zengwangfa/2019-Electronic-Design-Competition/docs/DataSheet/NB-IOT/3.8V供电接线原理图.png

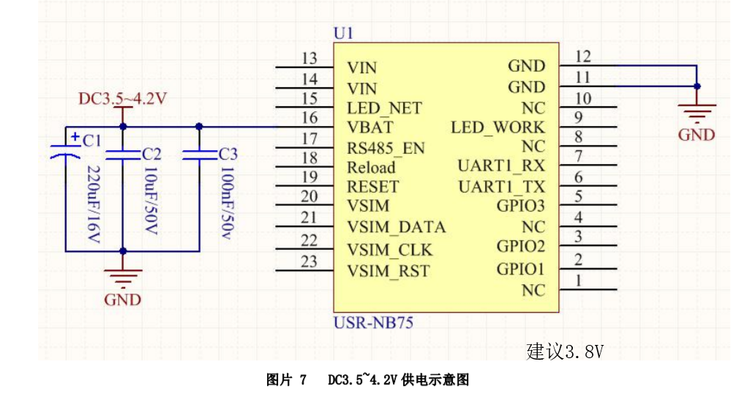
docs/DataSheet/NB-IOT/3.8V供电接线原理图.png
