zengwangfa/2019-Electronic-Design-Competition/docs/DataSheet/NB-IOT/3.8v供电注意事项.png

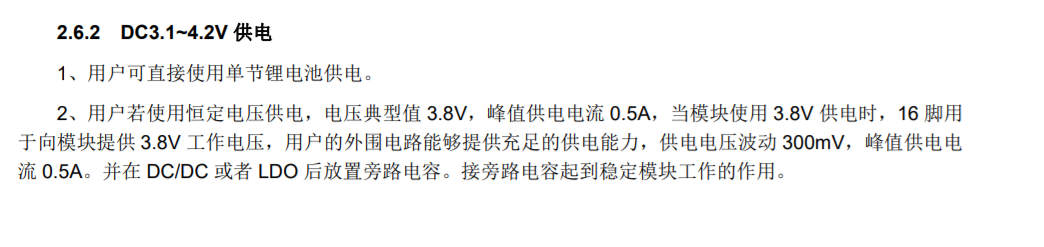
docs/DataSheet/NB-IOT/3.8v供电注意事项.png
