zengwangfa/2019-Electronic-Design-Competition/docs/DataSheet/NB-IOT/SIM卡引脚位.png

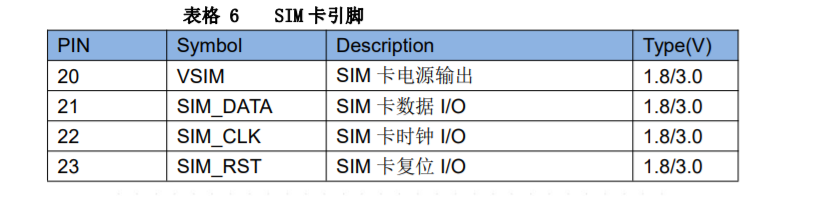
docs/DataSheet/NB-IOT/SIM卡引脚位.png
