zengwangfa/2019-Electronic-Design-Competition/docs/DataSheet/NB-IOT/串口.png

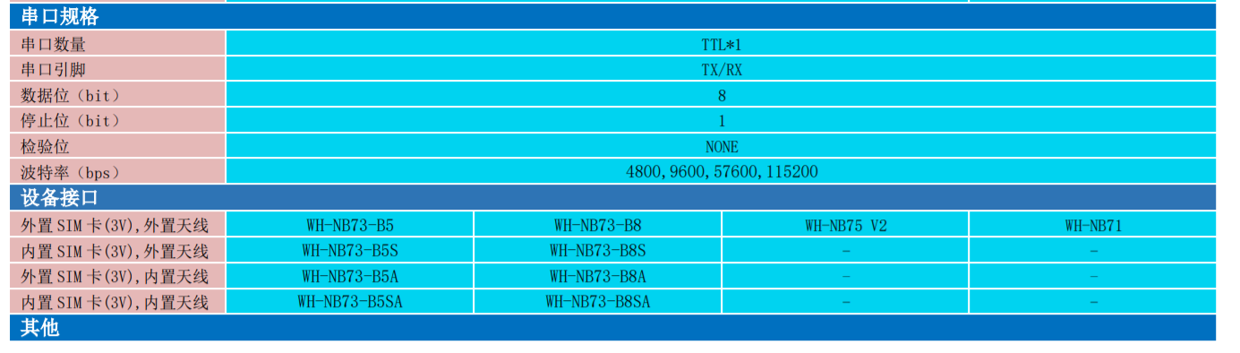
docs/DataSheet/NB-IOT/串口.png
