zengwangfa/2019-Electronic-Design-Competition/docs/DataSheet/NB-IOT/基本参数.png

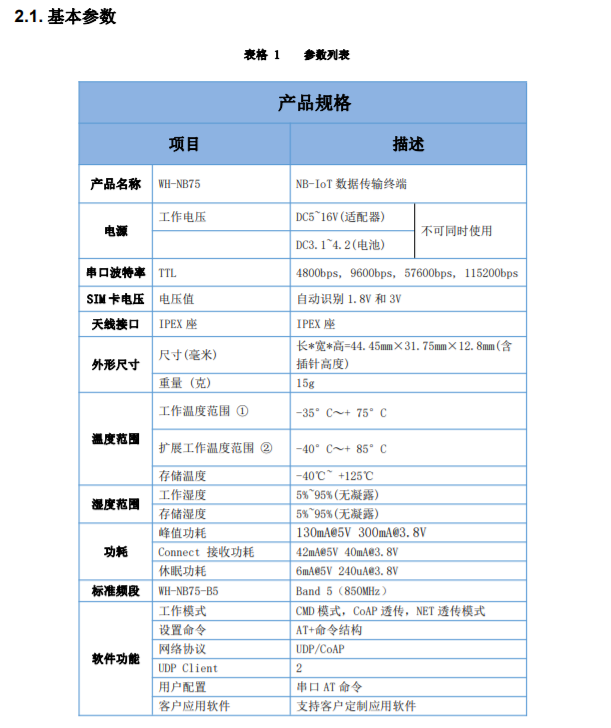
docs/DataSheet/NB-IOT/基本参数.png
