zengwangfa/2019-Electronic-Design-Competition/docs/DataSheet/NB-IOT/透传云注册.png

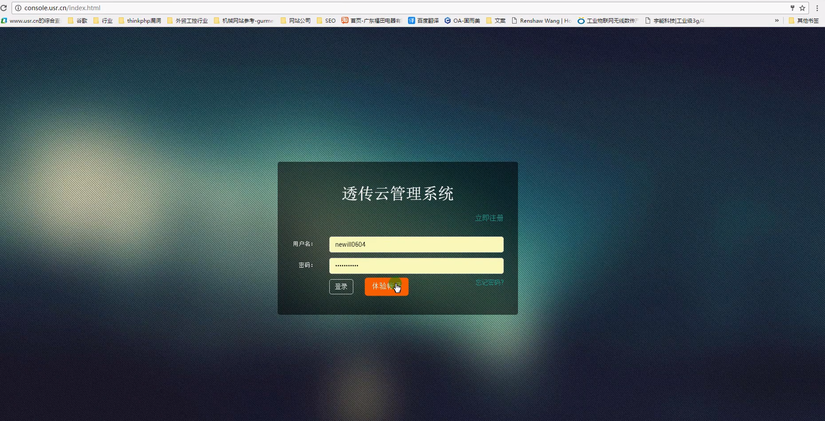
docs/DataSheet/NB-IOT/透传云注册.png
