zengwangfa/2019-Electronic-Design-Competition/docs/pictures/2017年全国大学生电子设计竞赛综合测评题.jpg

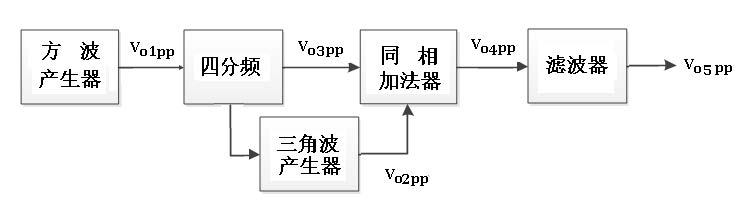
docs/pictures/2017年全国大学生电子设计竞赛综合测评题.jpg
