zengwangfa/2019-Electronic-Design-Competition/docs/pictures/2017综合测评题 (1).jpg

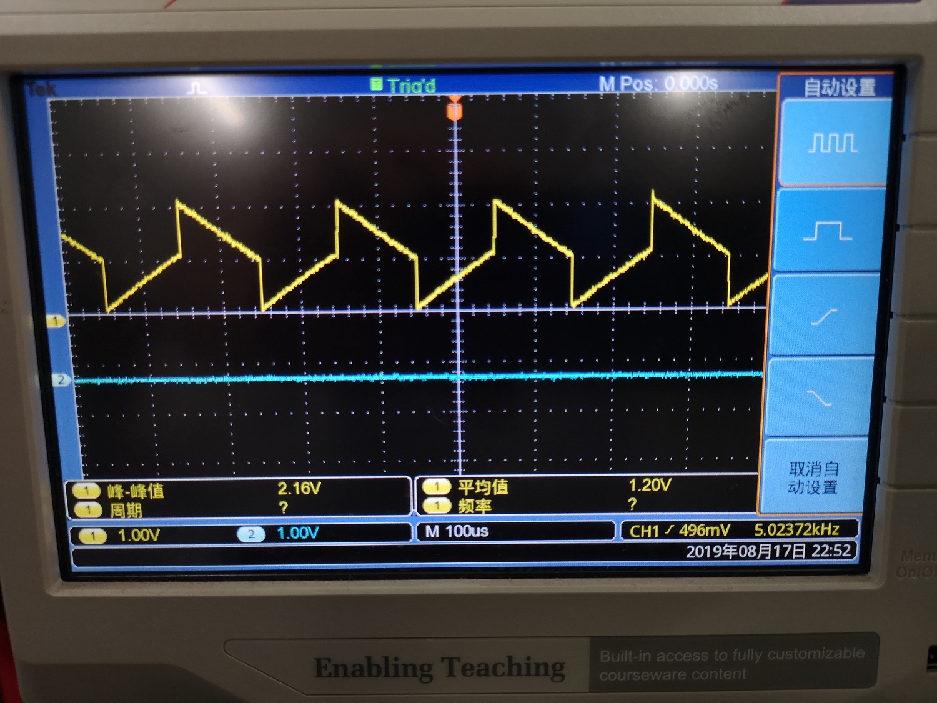
docs/pictures/2017综合测评题 (1).jpg
