zengwangfa/2019-Electronic-Design-Competition/docs/pictures/hmi/paper_hmi.gif

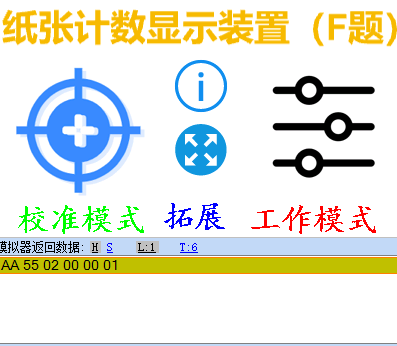
docs/pictures/hmi/paper_hmi.gif
