zengwangfa/2019-Electronic-Design-Competition/hmi/picture & font/picture (2).png

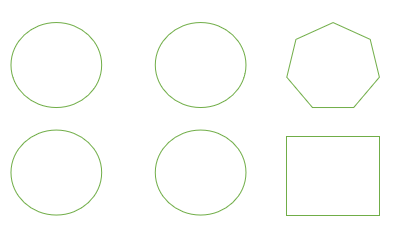
hmi/picture & font/picture (2).png
