zengwangfa/2019-Electronic-Design-Competition/hmi/picture & font/picture (3).png

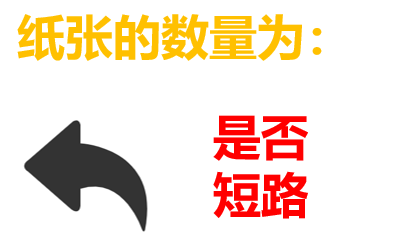
hmi/picture & font/picture (3).png
