zengwangfa/2019-Electronic-Design-Competition/hmi/picture & font/picture (4).png

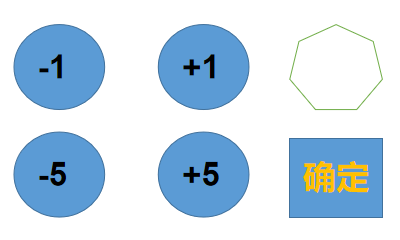
hmi/picture & font/picture (4).png
