zengwangfa/2019-Electronic-Design-Competition/hmi/picture & font/下降 (1).png

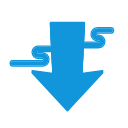
hmi/picture & font/下降 (1).png
