zengwangfa/2019-Electronic-Design-Competition/hmi/picture & font/减 (1) - 副本.png

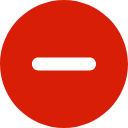
hmi/picture & font/减 (1) - 副本.png
