zengwangfa/2019-Electronic-Design-Competition/hmi/picture & font/加.png

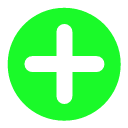
hmi/picture & font/加.png
