zengwangfa/2019-Electronic-Design-Competition/hmi/picture & font/升级 (4).png

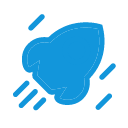
hmi/picture & font/升级 (4).png
