zengwangfa/2019-Electronic-Design-Competition/hmi/picture & font/原材料.png

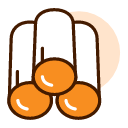
hmi/picture & font/原材料.png
