zengwangfa/2019-Electronic-Design-Competition/hmi/picture & font/手势单击系列.png

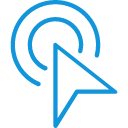
hmi/picture & font/手势单击系列.png
