zengwangfa/2019-Electronic-Design-Competition/hmi/picture & font/打印机.png

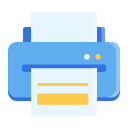
hmi/picture & font/打印机.png
