zengwangfa/2019-Electronic-Design-Competition/hmi/picture & font/按钮 (1).png

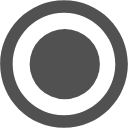
hmi/picture & font/按钮 (1).png
