zengwangfa/2019-Electronic-Design-Competition/hmi/picture & font/纸币 (1).png

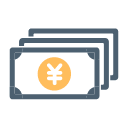
hmi/picture & font/纸币 (1).png
