zengwangfa/2019-Electronic-Design-Competition/hmi/picture & font/超级玛丽3.jpg

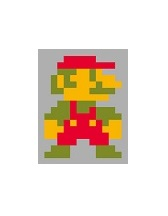
hmi/picture & font/超级玛丽3.jpg
