zengwangfa/2019-Electronic-Design-Competition/matlab/电容1.png

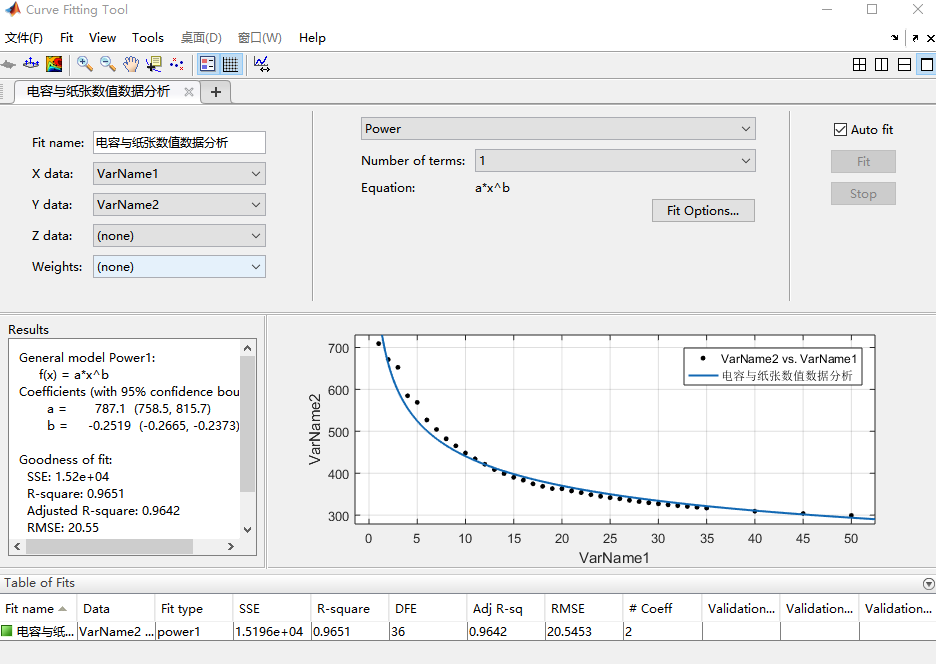
matlab/电容1.png
