zengwangfa/2019-Electronic-Design-Competition/matlab/电容2.png

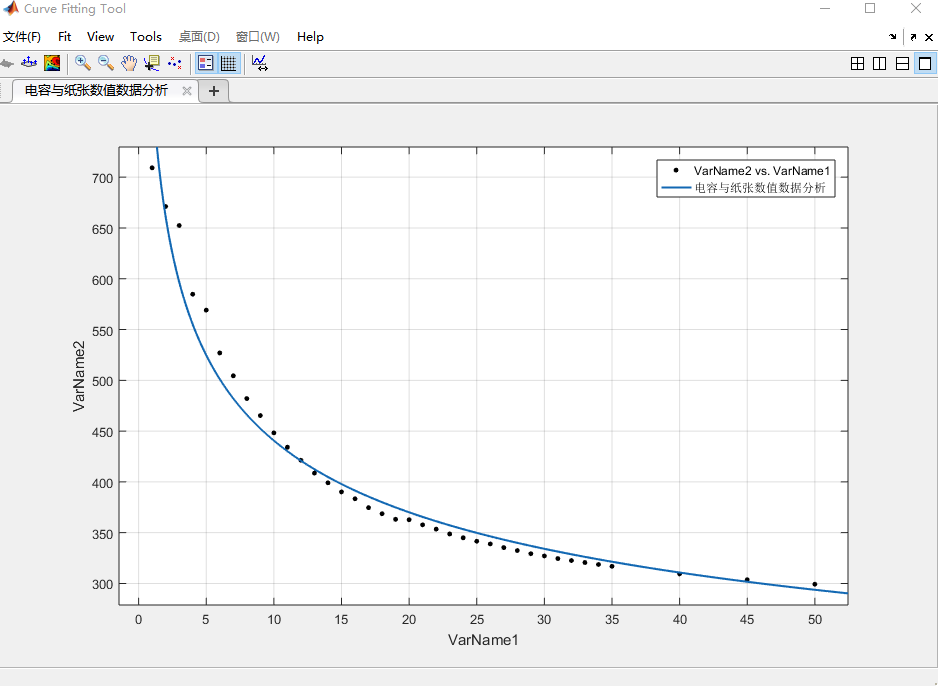
matlab/电容2.png
