zengwangfa/2019-Electronic-Design-Competition/matlab/纸张1.png

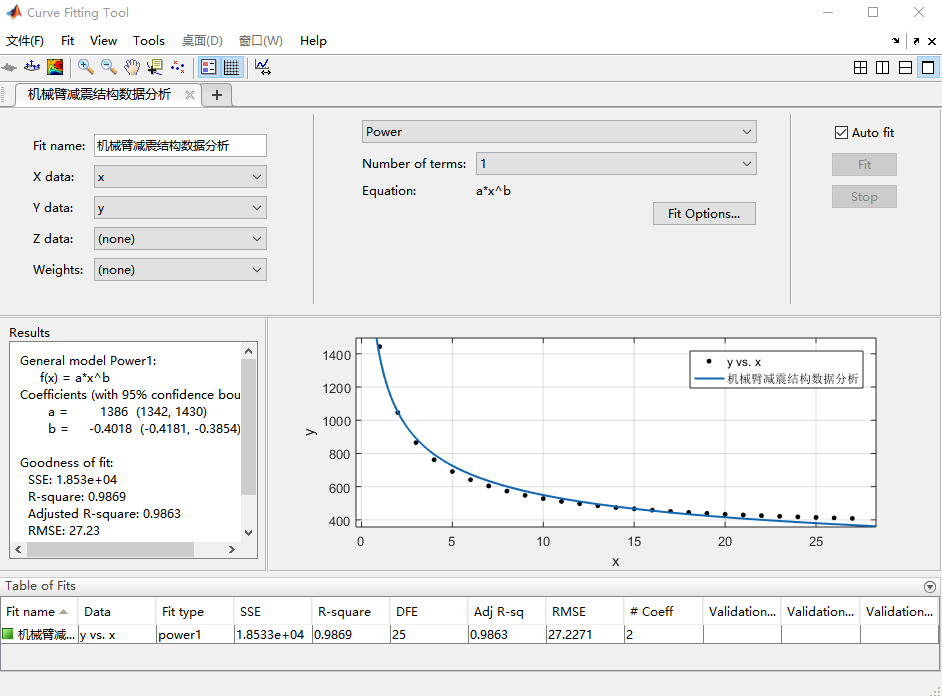
matlab/纸张1.png
