zengwangfa/2019-Electronic-Design-Competition/matlab/纸张2.png

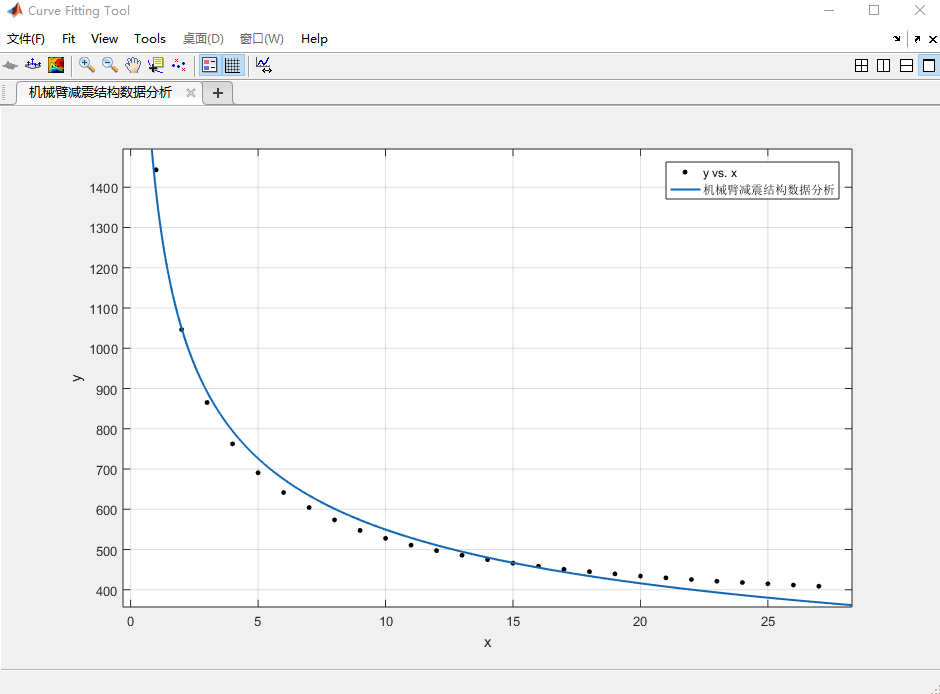
matlab/纸张2.png
