zengwangfa/2019-Electronic-Design-Competition/docs/pictures/debug.png

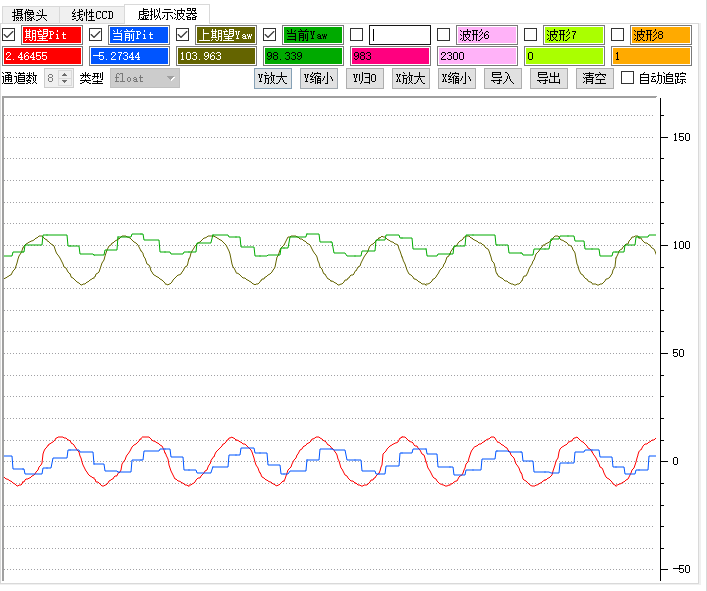
docs/pictures/debug.png
