zengwangfa/2019-Electronic-Design-Competition/others/software for development board/rt-thread-master/bsp/stm32f40x/applications/sensor.c

/*
 * servo.c
 *
 *  Created on: 2019年2月30日
 *      Author: zengwangfa
 *      Notes:  传感器设备【深度传感器、CPU参数、ADC电压】
 */
 
 #define LOG_TAG    "sensor"
#include "sensor.h"
#include <rtthread.h>
#include <elog.h>
#include <string.h>
#include "drv_MS5837.h"
#include "gyroscope.h"
#include "flash.h"
#include "stdio.h"
#include "drv_i2c.h"
#include "drv_adc.h"
#include "drv_cpu_temp.h"
#include "drv_cpuusage.h"
#include "filter.h"
#include "drv_spl1301.h"

/*----------------------- Variable Declarations -----------------------------*/
char *Depth_Sensor_Name[3] = {"MS5837","SPL1301","null"};

Sensor_Type Sensor;//传感器参数
		float temp_current = 0.0f;

/*----------------------- Function Implement --------------------------------*/
/**
  * @brief  sensor_lowSpeed_thread_entry(低速获取传感器任务函数)
  * @param  void* parameter
  * @retval None
  * @notice 
  */
void sensor_lowSpeed_thread_entry(void* parameter)
{
		uint8 cpu_usage_major, cpu_usage_minor; //整数位、小数位

		rt_thread_mdelay(1000);//等待3s系统稳定再获取数据

		while(1)
		{
			
				Sensor.CPU.Temperature = get_cpu_temp();           //获取CPU温度
				Sensor.PowerSource.Voltage = get_voltage_value();  //获取电源电压值
//				if(Sensor.PowerSource.Voltage > 6.0f ){							//当未接入电源时，不检测电流值
//						
//						Sensor.PowerSource.Current = get_current_value();  //获取INA169电流值
//						temp_current = Sensor.PowerSource.Current ;
//						Sensor.PowerSource.Current = KalmanFilter(&Sensor.PowerSource.Current);
//						 //电流值 进行卡尔曼滤波【该卡尔曼滤波调节r的值，滞后性相对较大】
//				}
				cpu_usage_get(&cpu_usage_major, &cpu_usage_minor); //获取CPU使用率
				Sensor.CPU.Usage = cpu_usage_major + (float)cpu_usage_minor/100;
			

				rt_thread_mdelay(100);
		}
}

/**
  * @brief  sensor_highSpeed_thread_entry(高速获取传感器任务函数)
  * @param  void* parameter
  * @retval None
  * @notice 
  */


void sensor_highSpeed_thread_entry(void* parameter)
{

		rt_thread_mdelay(1000);//等待3s系统稳定再获取数据
	
		while(1)
		{
			
				//JY901_Convert(&Sensor.JY901); //JY901数据转换
				//Depth_Sensor_Data_Convert();  //深度数据转换

				rt_thread_mdelay(20);
		}
}



/*******************************线程初始化*******************************************/
int sensor_thread_init(void)
{
    rt_thread_t sensor_lowSpeed_tid; //低速获取的传感器放入接口
	  rt_thread_t sensor_highSpeed_tid;//高速获取的传感器放入接口
		/*创建动态线程*/
    sensor_lowSpeed_tid = rt_thread_create("sensor",  //线程名称
                    sensor_lowSpeed_thread_entry,		 //线程入口函数【entry】
                    RT_NULL,							   //线程入口函数参数【parameter】
                    2048,										 //线程栈大小，单位是字节【byte】
                    30,										 	 //线程优先级【priority】
                    10);										 //线程的时间片大小【tick】= 100ms

	  sensor_highSpeed_tid = rt_thread_create("sensor",  //线程名称
                    sensor_highSpeed_thread_entry,		 //线程入口函数【entry】
                    RT_NULL,							   //线程入口函数参数【parameter】
                    2048,										 //线程栈大小，单位是字节【byte】
                    10,										 	 //线程优先级【priority】
                    3);										 //线程的时间片大小【tick】= 100ms

    if (sensor_lowSpeed_tid != RT_NULL && sensor_highSpeed_tid != RT_NULL){
			



				if(adc_init()){ log_i("Adc_Init()");}//ADC电压采集初始化

//				rt_thread_startup(sensor_lowSpeed_tid);
//				rt_thread_startup(sensor_highSpeed_tid);
		}
		return 0;
}
//INIT_APP_EXPORT(sensor_thread_init);


void Depth_Sensor_Data_Convert(void)//深度传感器数据转换
{
		static uint32 value[10] = {0};
		static uint8 ON_OFF = 0; //自锁开关
		static uint8 i = 0;
		
		if(SPL1301 == Sensor.DepthSensor.Type){  //歌尔 SPL1301
				spl1301_get_raw_temp();
				spl1301_get_raw_pressure();//传感器数据转换
				
				if(ON_OFF == 0){
						ON_OFF = 1;
						Sensor.DepthSensor.Init_PessureValue = get_spl1301_pressure();//获取初始化数据
				}
				for(i = 0;i < 10;i++){
						value[i++] = get_spl1301_pressure();//获取1次数据
				}
				Sensor.DepthSensor.Temperature = get_spl1301_temperature();
				Sensor.DepthSensor.PessureValue = Bubble_Filter(value);
								 				                              /* 深度数值 单位为cm   定标系数为 1.3 单位/cm */
				Sensor.DepthSensor.Depth = ((Sensor.DepthSensor.PessureValue - Sensor.DepthSensor.Init_PessureValue)/20);		
			 
		}
		else if(MS5837 == Sensor.DepthSensor.Type){ //使用MS5837
			
				if(ON_OFF == 0 ){
						ON_OFF = 1; //自锁开关																							       
						Sensor.DepthSensor.Init_PessureValue = get_ms5837_pressure();//获取初始化数据
				}		 
						
				Sensor.DepthSensor.PessureValue = get_ms5837_pressure();
				Sensor.DepthSensor.Temperature  = get_ms5837_temperature();

				//理想状态，深度传感器的压力值理应越来越大
				if(Sensor.DepthSensor.Init_PessureValue - Sensor.DepthSensor.PessureValue >= 1 && \
					 Sensor.DepthSensor.Init_PessureValue - Sensor.DepthSensor.PessureValue <= 5 ){	//若深度传感器 当前值逐渐变小，则判定为发生漂移，令初值等于当前值
			
						Sensor.DepthSensor.Init_PessureValue = Sensor.DepthSensor.PessureValue;
				}
					 				                              /* 深度数值 单位为cm   定标系数为 1.95 单位/cm */
				Sensor.DepthSensor.Depth = ((Sensor.DepthSensor.PessureValue - Sensor.DepthSensor.Init_PessureValue)/1.95f);			
		}

}


/* 打印传感器信息 */
void print_sensor_info(void)
{
		log_i("    variable        |  value");
		log_i("--------------------|-----------");
	
		log_i("      Roll          |  %+0.3f",Sensor.JY901.Euler.Roll);
		log_i("      Pitch         |  %+0.3f",Sensor.JY901.Euler.Pitch);
		log_i("      Yaw           |  %+0.3f",Sensor.JY901.Euler.Yaw);
		log_i("--------------------|-----------");
		log_i("      Acc.x         |  %+0.3f",Sensor.JY901.Acc.x);
		log_i("      Acc.y         |  %+0.3f",Sensor.JY901.Acc.y);//
		log_i("      Acc.z         |  %+0.3f",Sensor.JY901.Acc.z);//
		log_i("--------------------|-----------");
		log_i("      Gyro.x        |  %+0.3f",Sensor.JY901.Gyro.x);
		log_i("      Gyro.y        |  %+0.3f",Sensor.JY901.Gyro.y);//	
		log_i("      Gyro.z        |  %+0.3f",Sensor.JY901.Gyro.z);//	
		log_i("  JY901_Temperature |  %+0.3f",Sensor.JY901.Temperature);//					

	
		log_i("--------------------|-----------");
		log_i("     Voltage        |  %0.3f",Sensor.PowerSource.Voltage); //电压
		log_i("     Current        |  %0.3f",Sensor.PowerSource.Current); //电流
		log_i("--------------------|-----------");
		log_i("  Depth Sensor Type |  %s",Depth_Sensor_Name[Sensor.DepthSensor.Type]); //深度传感器类型
		log_i(" Water Temperature  |  %0.3f",Sensor.DepthSensor.Temperature);    //水温
		log_i("sensor_Init_Pressure|  %0.3f",Sensor.DepthSensor.Init_PessureValue); //深度传感器初始压力值	
		log_i("   sensor_Pressure  |  %0.3f",Sensor.DepthSensor.PessureValue); 		 //深度传感器当前压力值	
		log_i("     Depth          |  %0.3f",Sensor.DepthSensor.Depth); 									 //深度值
		log_i("--------------------|-----------");	
		log_i("    CPU.Usages      |  %0.3f",	Sensor.CPU.Temperature); //CPU温度
		log_i("   CPU.Temperature  |  %0.3f",	Sensor.CPU.Usage); 			 //CPU使用率

		

}
MSH_CMD_EXPORT(print_sensor_info, printf gysocope & PowerSource & pressure);



/*【深度传感器】 修改 【类型】MSH方法 */
static int set_depth_sensor_type(int argc, char **argv) //只能是 0~3.0f
{
    int result = 0;
    if (argc != 2){ //6个推进器
        log_e("Error! Proper Usage: set_depth_sensor_type <ms5837/spl1301/null>");
				result = -RT_ERROR;
        goto _exit;
    }
		
	  if( !strcmp(argv[1],"ms5837") ) {
				 
				Sensor.DepthSensor.Type = MS5837; //
				Flash_Update();
	
				log_i("Sensor.DepthSensor.Type :%s",Depth_Sensor_Name[Sensor.DepthSensor.Type]);
				log_i("Please reboot now");		
		}
	  else if( !strcmp(argv[1],"spl1301") ) {
				 
				Sensor.DepthSensor.Type = SPL1301; //
				Flash_Update();

				log_i("Sensor.DepthSensor.Type :%s",Depth_Sensor_Name[Sensor.DepthSensor.Type]);
				log_i("Please reboot now");				
		}	

	  else if( !strcmp(argv[1],"null") ) {
				 
				Sensor.DepthSensor.Type = DS_NULL; //无深度传感器
				Flash_Update();

				log_i("Sensor.DepthSensor.Type :%s",Depth_Sensor_Name[Sensor.DepthSensor.Type]);
				log_i("Please reboot now");				
		}				
		else {
				log_e("Error! Input Error!");
		}
_exit:
    return result;
}
MSH_CMD_EXPORT(set_depth_sensor_type,depth_sensor_type_set <ms5837/spl1301/null> );



/*【电源容量】 修改 【容量】MSH方法 */
static int set_battery_capacity(int argc, char **argv)
{
    int result = 0;
    if (argc != 2){ //6个推进器
        log_e("Error! Proper Usage: set_battery_capacity <2s/3s/4s/6s> % ");
				result = -RT_ERROR;
        goto _exit;
    }
		
	  if( !strcmp(argv[1],"2s") ) {
				 
				Sensor.PowerSource.Capacity = 4.2*2; // 2s->8.4v的满电压
				Flash_Update();
	
				log_i("Sensor.PowerSource.Capacity :%f v",Sensor.PowerSource.Capacity);
		}		
	  else if( !strcmp(argv[1],"3s") ) {
				 
				Sensor.PowerSource.Capacity = 4.2*3; // 3s->12.6v的满电压
				Flash_Update();
	
				log_i("Sensor.PowerSource.Capacity :%f v",Sensor.PowerSource.Capacity);
		}
	  else if( !strcmp(argv[1],"4s") ) {
				 
				Sensor.PowerSource.Capacity = 4.2*4; // 4s->16.8v的满电压
				Flash_Update();

				log_i("Sensor.PowerSource.Capacity :%f v",Sensor.PowerSource.Capacity);
		}		
		
		else if( !strcmp(argv[1],"6s") ) {
				 
				Sensor.PowerSource.Capacity = 4.2*6; // 6s->25.2v的满电压
				Flash_Update();

				log_i("Sensor.PowerSource.Capacity :%f v",Sensor.PowerSource.Capacity);
		}		
		else {
				log_e("Error! Input Error!");
		}
_exit:
    return result;
}
MSH_CMD_EXPORT(set_battery_capacity,set_battery_capacity <2s/3s/4s/6s> );
