zengwangfa/2019-Electronic-Design-Competition/others/software for development board/rt-thread-master/bsp/stm32f40x/applications/sensor.h

#ifndef __SENSOR_H_
#define __SENSOR_H_

#include "DataType.h"


/* 打印传感器信息 */
void print_sensor_info(void);
void Depth_Sensor_Data_Convert(void);//深度传感器数据转换

extern char *Depth_Sensor_Name[3];


#endif
