zengwangfa/2019-Electronic-Design-Competition/others/software for development board/rt-thread-master/bsp/stm32f40x/drivers/drv_ano.c

/*
 * File      : drv_ano.c
 * COPYRIGHT (C) 2019 JMU Electronic Technology Association Team 
 *
 * Change Logs:
 * Date         Author          Notes
 * 2019.3				zengwangfa      匿名地面站(ANO_TC)通信协议移植v1.0
 * 
 * Attention: 接收只需要调用 -> ANO_DT_Data_Receive_Prepare(uint8 data);
 *【统一接口】发送只需要调用 -> ANO_SEND_StateMachine(void);
 *            保存参数需调用 -> void Save_Or_Reset_PID_Parameter(void);
 */
#include <rtdevice.h>
#include <elog.h>
#include "drv_ano.h"
#include "sys.h"
#include "PID.h"
#include "led.h"
#include "flash.h"
#include "gyroscope.h"
#include "rc_data.h"
#include "propeller.h"
#include <ioDevices.h>

/*---------------------- Constant / Macro Definitions -----------------------*/		

#define BYTE0(dwTemp)       ( *( (char *)(&dwTemp) + 0) )
#define BYTE1(dwTemp)       ( *( (char *)(&dwTemp) + 1) )
#define BYTE2(dwTemp)       ( *( (char *)(&dwTemp) + 2) )
#define BYTE3(dwTemp)       ( *( (char *)(&dwTemp) + 3) )
	


#define HardwareType 	0.00  //硬件种类  00为其他硬件版本
#define HardwareVER 	2.00  //硬件版本
#define SoftwareVER 	7.50  //软件版本  7月5日
#define ProtocolVER 	1  		//协议版本
#define BootloaderVER 1  		//Bootloader版本
/*----------------------- Variable Declarations. -----------------------------*/

extern rt_device_t debug_uart_device;	
extern float  volatge;
extern ReceiveData_Type ReceiveData;

Vector3f_pid PID_Parameter[PID_USE_NUM]={0};
uint8 data_to_send[50];//ANO地面站发送数据缓冲
uint8 ANO_Send_PID_Flag[6]={0};//PID发送标志位

uint8 Sort_PID_Cnt=0;
uint8 Sort_PID_Flag=0; //PID状态标志位：1存FLASH  2复位原始数据


//---------------这里是分隔符↓↓↓↓↓↓↓↓↓↓<以下为接收 函数>↓↓↓↓↓↓↓↓↓↓这里是分隔符------------------//
/*******************************************
* 函 数 名：ANO_DT_Data_Receive_Prepare
* 功    能：ANO地面站数据解析
* 输入参数：串口循环传入的一个数据data
* 返 回 值：none
* 注    意：none
********************************************/
void ANO_DT_Data_Receive_Prepare(uint8 data)//ANO地面站数据解析
{
		static uint8 RxBuffer[50];
		static uint8 _data_len = 0,_data_cnt = 0;
		static uint8 state = 0;
		if(state==0&&data==0xAA)//帧头1
		{
				state=1;
				RxBuffer[0]=data;
		}
		else if(state==1&&data==0xAF)//帧头2
		{
				state=2;
				RxBuffer[1]=data;
		}
		else if(state==2&&data<0XF1)//功能字节
		{
				state=3;
				RxBuffer[2]=data;
		}
		else if(state==3&&data<50)//有效数据长度
		{
				state = 4;
				RxBuffer[3]=data;
				_data_len = data;
				_data_cnt = 0;
		}
		else if(state==4&&_data_len>0)//数据接收
		{
				_data_len--;
				RxBuffer[4+_data_cnt++]=data;
				if(_data_len==0)
					state = 5;
		}
		else if(state==5)//校验和
		{
				state = 0;
				RxBuffer[4+_data_cnt]=data;
				ANO_DT_Data_Receive_Anl(RxBuffer,_data_cnt+5);//数据解析
		}
		else state = 0;
}



/*******************************************
* 函 数 名：ANO_DT_Send_Check
* 功    能：ANO地面站和校验
* 输入参数：head 功能字
						check_num 校验和
* 返 回 值：none
* 注    意：none
********************************************/
static void ANO_DT_Send_Check(uint8 head, uint8 check_sum)
{
		uint8 sum = 0,i=0;
		data_to_send[0]=0xAA;
		data_to_send[1]=0xAA;
		data_to_send[2]=0xEF;
		data_to_send[3]=2;
		data_to_send[4]=head;
		data_to_send[5]=check_sum;
		for(i=0;i<6;i++){
				sum += data_to_send[i];
		}
		data_to_send[6]=sum;
		rt_device_write(debug_uart_device, 0,data_to_send, 7);    //发送后命令

}

/*******************************************
* 函 数 名：ANO_DT_Data_Receive_Anl
* 功    能：ANO数据解析
* 输入参数：data_buf: 数据包
						num: 数据包大小
* 返 回 值：none
* 注    意：none
********************************************/
void ANO_DT_Data_Receive_Anl(uint8 *data_buf,uint8 num)
{
		uint8 sum = 0,i=0;
		for(i=0;i<(num-1);i++)  sum += *(data_buf+i);
		if(!(sum==*(data_buf+num-1)))    return; //判断sum
		if(!(*(data_buf)==0xAA && *(data_buf+1)==0xAF))     return;//判断帧头
		if(*(data_buf+2)==0x01)
		{
				if(*(data_buf+4)==0x01) {;}
				if(*(data_buf+4)==0x02) {;}
				if(*(data_buf+4)==0x03) {;}
		}
		
		if(*(data_buf+2)==0x02)
		{
				if(*(data_buf+4)==0x01)		//读取当前PID参数
				{
						ANO_Send_PID_Flag[0]=1;
						ANO_Send_PID_Flag[1]=1;
						ANO_Send_PID_Flag[2]=1;
						ANO_Send_PID_Flag[3]=1;
						ANO_Send_PID_Flag[4]=1;
						ANO_Send_PID_Flag[5]=1;
				
						Bling_Set(&Light_Red,300,50,0.5,0,77,0);
						Bling_Set(&Light_Green,300,100,0.5,0,78,0);
				}
				if(*(data_buf+4)==0x02)//读取飞行模式设置请求
				{
						;
				}
				if(*(data_buf+4)==0xA0)//读取下位机版本信息
				{
						;
				}
				if(*(data_buf+4)==0xA1)//恢复默认参数
				{
						Sort_PID_Flag = 2;	
						Bling_Set(&Light_Green,300,50,0.5,0,78,0);
						Bling_Set(&Light_Blue,300,100,0.5,0,79,0);
				}
		}
		
		if(*(data_buf+2)==0x10)                             //接收PID1
		{
				Total_Controller.Roll_Gyro_Control.Kp  = 0.001*( (vs16)(*(data_buf+4)<<8)|*(data_buf+5) );
				Total_Controller.Roll_Gyro_Control.Ki  = 0.001*( (vs16)(*(data_buf+6)<<8)|*(data_buf+7) );
				Total_Controller.Roll_Gyro_Control.Kd  = 0.01 *( (vs16)(*(data_buf+8)<<8)|*(data_buf+9) );
				Total_Controller.Pitch_Gyro_Control.Kp = 0.001*( (vs16)(*(data_buf+10)<<8)|*(data_buf+11) );
				Total_Controller.Pitch_Gyro_Control.Ki = 0.001*( (vs16)(*(data_buf+12)<<8)|*(data_buf+13) );
				Total_Controller.Pitch_Gyro_Control.Kd = 0.01 *( (vs16)(*(data_buf+14)<<8)|*(data_buf+15) );
				Total_Controller.Yaw_Gyro_Control.Kp   = 0.001*( (vs16)(*(data_buf+16)<<8)|*(data_buf+17) );
				Total_Controller.Yaw_Gyro_Control.Ki   = 0.001*( (vs16)(*(data_buf+18)<<8)|*(data_buf+19) );
				Total_Controller.Yaw_Gyro_Control.Kd   = 0.01 *( (vs16)(*(data_buf+20)<<8)|*(data_buf+21) );
				ANO_DT_Send_Check(*(data_buf+2),sum);
		}
		if(*(data_buf+2)==0x11)                             //接收PID2
		{
				Total_Controller.Roll_Angle_Control.Kp  = 0.001*( (vs16)(*(data_buf+4)<<8)|*(data_buf+5) );
				Total_Controller.Roll_Angle_Control.Ki  = 0.001*( (vs16)(*(data_buf+6)<<8)|*(data_buf+7) );
				Total_Controller.Roll_Angle_Control.Kd  = 0.01 *( (vs16)(*(data_buf+8)<<8)|*(data_buf+9) );
				Total_Controller.Pitch_Angle_Control.Kp = 0.001*( (vs16)(*(data_buf+10)<<8)|*(data_buf+11) );
				Total_Controller.Pitch_Angle_Control.Ki = 0.001*( (vs16)(*(data_buf+12)<<8)|*(data_buf+13) );
				Total_Controller.Pitch_Angle_Control.Kd = 0.01 *( (vs16)(*(data_buf+14)<<8)|*(data_buf+15) );
				Total_Controller.Yaw_Angle_Control.Kp   = 0.001*( (vs16)(*(data_buf+16)<<8)|*(data_buf+17) );
				Total_Controller.Yaw_Angle_Control.Ki   = 0.001*( (vs16)(*(data_buf+18)<<8)|*(data_buf+19) );
				Total_Controller.Yaw_Angle_Control.Kd   = 0.01 *( (vs16)(*(data_buf+20)<<8)|*(data_buf+21) );
				ANO_DT_Send_Check(*(data_buf+2),sum); 
		}
		if(*(data_buf+2)==0x12)                             //接收PID3
		{
				Total_Controller.High_Speed_Control.Kp    = 0.001*( (vs16)(*(data_buf+4)<<8)|*(data_buf+5) );
				Total_Controller.High_Speed_Control.Ki    = 0.001*( (vs16)(*(data_buf+6)<<8)|*(data_buf+7) );
				Total_Controller.High_Speed_Control.Kd    = 0.01 *( (vs16)(*(data_buf+8)<<8)|*(data_buf+9) );
				Total_Controller.High_Position_Control.Kp = 0.001*( (vs16)(*(data_buf+10)<<8)|*(data_buf+11) );
				Total_Controller.High_Position_Control.Ki = 0.001*( (vs16)(*(data_buf+12)<<8)|*(data_buf+13) );
				Total_Controller.High_Position_Control.Kd = 0.01 *( (vs16)(*(data_buf+14)<<8)|*(data_buf+15) );
				ANO_DT_Send_Check(*(data_buf+2),sum); 
		}
		if(*(data_buf+2)==0x13)                             //接收PID4
		{
				ANO_DT_Send_Check(*(data_buf+2),sum);
		}
		if(*(data_buf+2)==0x14)                             //接收PID5 【改为推进器方向标志】
		{

			
				ANO_DT_Send_Check(*(data_buf+2),sum);
		}
		if(*(data_buf+2)==0x15)                             //接收PID6  【改为推进器方向标志】
		{
			
				ANO_DT_Send_Check(*(data_buf+2),sum);
				Sort_PID_Cnt++;
				Sort_PID_Flag=1;
				Bling_Set(&Light_Red,300,50,0.5,0,77,0);
				Bling_Set(&Light_Blue,300,100,0.5,0,79,0);
		}
}

//---------------这里是分隔符↓↓↓↓↓↓↓↓↓↓<以下为发送 子函数>↓↓↓↓↓↓↓↓↓↓这里是分隔符------------------//
/*******************************************
* 函 数 名：ANO_Data_Send_Version
* 功    能：发送基本版本信息（硬件种类、硬件、软件、协议、Bootloader版本）【第一组】
* 输入参数：none
* 返 回 值：none
* 注    意：none
********************************************/
void ANO_Data_Send_Version(int hardwareType,int hardwareVER,int softwareVER,int protocolVER,int bootloaderVER)//发送版本信息
{
		uint8 _cnt=0;
		vs16 _temp;
		vs32 _temp2;
		uint8 sum = 0;
		uint8 i = 0;
		data_to_send[_cnt++]=0xAA;
		data_to_send[_cnt++]=0xAA;
		data_to_send[_cnt++]=0x00;
		data_to_send[_cnt++]=0;
		
		_temp = HardwareType;
		data_to_send[_cnt++]=BYTE0(_temp);
		_temp = (int)(HardwareVER*100);
		data_to_send[_cnt++]=BYTE1(_temp);
		data_to_send[_cnt++]=BYTE0(_temp);
		_temp = (int)(SoftwareVER*100);
		data_to_send[_cnt++]=BYTE1(_temp);
		data_to_send[_cnt++]=BYTE0(_temp);
		
		_temp2 = (int)(ProtocolVER*100);//单位cm
		data_to_send[_cnt++]=BYTE1(_temp2);
		data_to_send[_cnt++]=BYTE0(_temp2);
		
		_temp2 = (int)(BootloaderVER*100);//单位cm  MS5837_Pressure
		data_to_send[_cnt++]=BYTE1(_temp2);
		data_to_send[_cnt++]=BYTE0(_temp2);

		
		data_to_send[3] = _cnt-4;
		sum = 0;
		for(i=0;i<_cnt;i++){
				sum += data_to_send[i];
		}
		data_to_send[_cnt++]=sum;
		rt_device_write(debug_uart_device, 0,data_to_send, _cnt);    //发送后命令
}


/*******************************************
* 函 数 名：ANO_Data_Send_Status
* 功    能：发送基本信息（欧拉三角、高度、锁定状态）【第二组】
* 输入参数：none
* 返 回 值：none
* 注    意：none
********************************************/
void ANO_Data_Send_Status(int roll,int pitch,int yaw,int depth)//发送基本信息（姿态、锁定状态）
{
		uint8 _cnt=0;
		vs16 _temp;
		vs32 _temp2;
		uint8 sum = 0;
		uint8 i;
		data_to_send[_cnt++]=0xAA;
		data_to_send[_cnt++]=0xAA;
		data_to_send[_cnt++]=0x01;
		data_to_send[_cnt++]=0;
		
		_temp = (int)(roll*100);
		data_to_send[_cnt++]=BYTE1(_temp);
		data_to_send[_cnt++]=BYTE0(_temp);
		_temp = (int)(pitch*100);
		data_to_send[_cnt++]=BYTE1(_temp);
		data_to_send[_cnt++]=BYTE0(_temp);
		_temp = (int)(yaw*100);
		data_to_send[_cnt++]=BYTE1(_temp);
		data_to_send[_cnt++]=BYTE0(_temp);
		
		_temp2 = (int)(depth);//单位cm
		data_to_send[_cnt++]=BYTE3(_temp2);
		data_to_send[_cnt++]=BYTE2(_temp2);
		data_to_send[_cnt++]=BYTE1(_temp2);
		data_to_send[_cnt++]=BYTE0(_temp2);
		
		data_to_send[_cnt++]=0x01;//飞行模式
		data_to_send[_cnt++]=2-ControlCmd.All_Lock;//【匿名】上锁0、解锁1   自定义为：0x01解锁，0x02上锁
   		
		data_to_send[3] = _cnt-4;
		sum = 0;
		for(i=0;i<_cnt;i++){
				sum += data_to_send[i];
		}
		data_to_send[_cnt++]=sum;
		rt_device_write(debug_uart_device, 0,data_to_send, _cnt);    //发送后命令
}

/*******************************************
* 函 数 名：ANO_DT_Send_Senser
* 功    能：发送传感器原始数字量 (加速度、角速度、磁场)  【第三组】
* 输入参数：3组数据x,y,z轴
* 返 回 值：none
* 注    意：none
********************************************/
void ANO_DT_Send_Senser(float a_x,float a_y,float a_z,float g_x,float g_y,float g_z,float m_x,float m_y,float m_z)
{
		uint8 _cnt=0;
		vs16 _temp;
		uint8 sum = 0;
		uint8 i = 0;
		data_to_send[_cnt++]=0xAA;
		data_to_send[_cnt++]=0xAA;
		data_to_send[_cnt++]=0x02;
		data_to_send[_cnt++]=0;
		
		_temp = (int)(a_x*100);   
		data_to_send[_cnt++]=BYTE1(_temp);
		data_to_send[_cnt++]=BYTE0(_temp);
		_temp = (int)(a_y*100);
		data_to_send[_cnt++]=BYTE1(_temp);
		data_to_send[_cnt++]=BYTE0(_temp);
		_temp = (int)(a_z*100);
		data_to_send[_cnt++]=BYTE1(_temp);
		data_to_send[_cnt++]=BYTE0(_temp);
		
		_temp = g_x;
		data_to_send[_cnt++]=BYTE1(_temp);
		data_to_send[_cnt++]=BYTE0(_temp);
		_temp = g_y;
		data_to_send[_cnt++]=BYTE1(_temp);
		data_to_send[_cnt++]=BYTE0(_temp);
		_temp = g_z;
		data_to_send[_cnt++]=BYTE1(_temp);
		data_to_send[_cnt++]=BYTE0(_temp);
		
		_temp = m_x;
		data_to_send[_cnt++]=BYTE1(_temp);
		data_to_send[_cnt++]=BYTE0(_temp);
		_temp = m_y;
		data_to_send[_cnt++]=BYTE1(_temp);
		data_to_send[_cnt++]=BYTE0(_temp);
		_temp = m_z;
		data_to_send[_cnt++]=BYTE1(_temp);
		data_to_send[_cnt++]=BYTE0(_temp);
		
		data_to_send[3] = _cnt-4;
		
		sum = 0;
		for(i=0;i<_cnt;i++){
				sum += data_to_send[i];
		}
		data_to_send[_cnt++] = sum;
		
		rt_device_write(debug_uart_device, 0,data_to_send, _cnt);    //发送后命令
}


/*******************************************
* 函 数 名：ANO_DT_Send_High
* 功    能：发送高度数据 (气压计高度、超声波高低)  【第七组】
* 输入参数：pressure_high：气压计高度、ultrasonic_high：超声波高度
* 返 回 值：none
* 注    意：none
********************************************/
void ANO_DT_Send_High(int pressure_high,u16 ultrasonic_high)
{
		uint8 _cnt=0;
		int _temp;
		u16 _temp2;
		uint8 sum = 0;
		uint8 i = 0;
		data_to_send[_cnt++]=0xAA;
		data_to_send[_cnt++]=0xAA;
		data_to_send[_cnt++]=0x07;
		data_to_send[_cnt++]=0;
		
		_temp = (int)(pressure_high);   
		data_to_send[_cnt++]=BYTE3(_temp);
		data_to_send[_cnt++]=BYTE2(_temp);
		data_to_send[_cnt++]=BYTE1(_temp);
		data_to_send[_cnt++]=BYTE0(_temp);
	
		_temp2 = (int)(ultrasonic_high*100);
		data_to_send[_cnt++]=BYTE1(_temp2);
		data_to_send[_cnt++]=BYTE0(_temp2);
	
		data_to_send[3] = _cnt-4;	
		sum = 0;
		for(i=0;i<_cnt;i++){
				sum += data_to_send[i];
		}
		data_to_send[_cnt++] = sum;
		
		rt_device_write(debug_uart_device, 0,data_to_send, _cnt);    //发送后命令
}

/*******************************************
* 函 数 名：ANO_DT_Send_PID
* 功    能：发送PID数据
* 输入参数：group:第几组PID数据
						3组PID数据p,i,d
* 返 回 值：none
* 注    意：第一组PID数据：group=1;
						以此类推
********************************************/
void ANO_DT_Send_PID(uint8 group,float p1_p,float p1_i,float p1_d,float p2_p,float p2_i,float p2_d,float p3_p,float p3_i,float p3_d)
{
		uint8 _cnt=0;
		uint8 sum = 0,i=0;
		int16_t _temp;
		
		data_to_send[_cnt++]=0xAA;
		data_to_send[_cnt++]=0xAA;
		data_to_send[_cnt++]=0x10+group-1;
		data_to_send[_cnt++]=0;
			
		_temp = (int16_t)(p1_p * 1000);
		data_to_send[_cnt++]=BYTE1(_temp);
		data_to_send[_cnt++]=BYTE0(_temp);
		_temp = (int16_t)(p1_i  * 1000);
		data_to_send[_cnt++]=BYTE1(_temp);
		data_to_send[_cnt++]=BYTE0(_temp);
		_temp = (int16_t)(p1_d  * 100);
		data_to_send[_cnt++]=BYTE1(_temp);
		data_to_send[_cnt++]=BYTE0(_temp);
		_temp = (int16_t)(p2_p  * 1000);
		data_to_send[_cnt++]=BYTE1(_temp);
		data_to_send[_cnt++]=BYTE0(_temp);
		_temp = (int16_t)(p2_i  * 1000);
		data_to_send[_cnt++]=BYTE1(_temp);
		data_to_send[_cnt++]=BYTE0(_temp);
		_temp = (int16_t)(p2_d * 100);
		data_to_send[_cnt++]=BYTE1(_temp);
		data_to_send[_cnt++]=BYTE0(_temp);
		_temp = (int16_t)(p3_p  * 1000);
		data_to_send[_cnt++]=BYTE1(_temp);
		data_to_send[_cnt++]=BYTE0(_temp);
		_temp = (int16_t)(p3_i  * 1000);
		data_to_send[_cnt++]=BYTE1(_temp);
		data_to_send[_cnt++]=BYTE0(_temp);
		_temp = (int16_t)(p3_d * 100);
		data_to_send[_cnt++]=BYTE1(_temp);
		data_to_send[_cnt++]=BYTE0(_temp);
		
		data_to_send[3] = _cnt-4;
		
		for(i=0;i<_cnt;i++){
			sum += data_to_send[i];
		}
		
		data_to_send[_cnt++]=sum;
		rt_device_write(debug_uart_device, 0,data_to_send, _cnt);    //发送后命令
}

/*******************************************
* 函 数 名：ANO_DT_Send_RCData
* 功    能：发送PID数据
* 输入参数：group:第几组PID数据
						3组PID数据p,i,d
* 返 回 值：none
* 注    意：第一组PID数据：group=1;
********************************************/
void ANO_DT_Send_RCData(u16 thr,u16 yaw,u16 rol,u16 pit,u16 aux1,u16 aux2,u16 aux3,u16 aux4,u16 aux5,u16 aux6)//发送遥控器通道数据
{
		uint8 _cnt=0;
		uint8 i=0;
		uint8 sum = 0;
		data_to_send[_cnt++]=0xAA;
		data_to_send[_cnt++]=0xAA;
		data_to_send[_cnt++]=0x03;
		data_to_send[_cnt++]=0;
		data_to_send[_cnt++]=BYTE1(thr);
		data_to_send[_cnt++]=BYTE0(thr);
		data_to_send[_cnt++]=BYTE1(yaw);
		data_to_send[_cnt++]=BYTE0(yaw);
		data_to_send[_cnt++]=BYTE1(rol);
		data_to_send[_cnt++]=BYTE0(rol);
		data_to_send[_cnt++]=BYTE1(pit);
		data_to_send[_cnt++]=BYTE0(pit);
		data_to_send[_cnt++]=BYTE1(aux1);
		data_to_send[_cnt++]=BYTE0(aux1);
		data_to_send[_cnt++]=BYTE1(aux2);
		data_to_send[_cnt++]=BYTE0(aux2);
		data_to_send[_cnt++]=BYTE1(aux3);
		data_to_send[_cnt++]=BYTE0(aux3);
		data_to_send[_cnt++]=BYTE1(aux4);
		data_to_send[_cnt++]=BYTE0(aux4);
		data_to_send[_cnt++]=BYTE1(aux5);
		data_to_send[_cnt++]=BYTE0(aux5);
		data_to_send[_cnt++]=BYTE1(aux6);
		data_to_send[_cnt++]=BYTE0(aux6);
		
		data_to_send[3] = _cnt-4;	
		sum = 0;
		for(i=0;i<_cnt;i++){
				sum += data_to_send[i];
		}
		data_to_send[_cnt++]=sum;
		rt_device_write(debug_uart_device, 0,data_to_send, _cnt);    //发送后命令
}

/*******************************************
* 函 数 名：ANO_Data_Send_Voltage_Current
* 功    能：发送电压、电流【第5组】
* 输入参数：电压、电流
* 返 回 值：none
* 注    意：none
********************************************/
void ANO_Data_Send_Voltage_Current(float volatge,float current)
{
		uint8 _cnt=0;
		vs16 _temp;
		vs32 _temp2;
		uint8 sum = 0;
		uint8 i = 0;
		data_to_send[_cnt++]=0xAA;
		data_to_send[_cnt++]=0xAA;
		data_to_send[_cnt++]=0x05;
		data_to_send[_cnt++]=0;
		
		_temp = (int)(volatge*100);      //电压
		data_to_send[_cnt++]=BYTE1(_temp);
		data_to_send[_cnt++]=BYTE0(_temp);
	
		_temp = (int)(current*100); //电流
		data_to_send[_cnt++]=BYTE1(_temp);
		data_to_send[_cnt++]=BYTE0(_temp);
			
		data_to_send[3] = _cnt-4;
		sum = 0;
		for(i=0;i<_cnt;i++){
				sum += data_to_send[i];
		}
		data_to_send[_cnt++]=sum;
		rt_device_write(debug_uart_device, 0,data_to_send, _cnt);    //发送后命令
}




//---------------这里是分隔符↓↓↓↓↓↓↓↓↓↓<以下为发送 子函数>↓↓↓↓↓↓↓↓↓↓这里是分隔符------------------//
/*******************************************
* 函 数 名：ANO_SEND_StateMachine
* 功    能：各组数据循环发送
* 输入参数：none
* 返 回 值：none
* 注    意：none
********************************************/
void ANO_SEND_StateMachine(void)
{
		static u16 ANO_Cnt = 0;

		if(ANO_Cnt == 0){
				//ANO_Data_Send_Version((int)HardwareType,(int)HardwareVER,(int)SoftwareVER,(int)ProtocolVER,(int)BootloaderVER);//发送基本版本信息（硬件种类、硬件、软件、协议、Bootloader版本）【第一组】
		}
		ANO_Cnt++;
		
		if(ANO_Cnt == 1){		
				//ANO_Data_Send_Status(Sensor.JY901.Euler.Roll,Sensor.JY901.Euler.Pitch,-Sensor.JY901.Euler.Yaw,Sensor.DepthSensor.Depth); //发送基本信息（欧拉三角、高度、锁定状态）【第二组】
		}
	
		else if(ANO_Cnt == 2){//发送传感器原始数字量 (加速度、角速度、磁场)  【第三组】
//				ANO_DT_Send_Senser(Sensor.JY901.Acc.x,Sensor.JY901.Acc.y,Sensor.JY901.Acc.z,
//													 Sensor.JY901.Gyro.x,Sensor.JY901.Gyro.y,Sensor.JY901.Gyro.z,
//													 Sensor.JY901.Mag.x,Sensor.JY901.Mag.y,Sensor.JY901.Mag.z);
		}
		
		else if(ANO_Cnt==3)
		{
//				ANO_DT_Send_RCData(PropellerPower.leftUp+1500,PropellerPower.rightUp+1500,
//													 PropellerPower.leftDown+1500,PropellerPower.rightDown+1500,
//													 PropellerPower.leftMiddle+1500,PropellerPower.rightMiddle+1500,
//													 0,0,0,0);
		}
		else if(ANO_Cnt == 4){
				//ANO_Data_Send_Voltage_Current(Sensor.PowerSource.Voltage,Sensor.PowerSource.Current);
		}
		
		else if(ANO_Cnt == 5) //发送高度数据 (气压计高度、超声波高低)  【第七组】
		{
				//ANO_DT_Send_High(Sensor.DepthSensor.PessureValue,0); //发送高度数据 (气压计高度、超声波高低)
		}

		else if(ANO_Cnt == 6 //发送PID数据
          &&ANO_Send_PID_Flag[0] == 0
            &&ANO_Send_PID_Flag[1] == 0
              &&ANO_Send_PID_Flag[2] == 0
                &&ANO_Send_PID_Flag[3] == 0
                  &&ANO_Send_PID_Flag[4] == 0
                    &&ANO_Send_PID_Flag[5] == 0)//提前终止发送队列
		{
				ANO_Cnt=0;
		}
	

		else if(ANO_Cnt == 7 && ANO_Send_PID_Flag[0] == 1){//第1帧 PID
				ANO_DT_Send_PID(1,Total_Controller.Roll_Gyro_Control.Kp, 
												Total_Controller.Roll_Gyro_Control.Ki,
												Total_Controller.Roll_Gyro_Control.Kd,
												Total_Controller.Pitch_Gyro_Control.Kp,
												Total_Controller.Pitch_Gyro_Control.Ki,
												Total_Controller.Pitch_Gyro_Control.Kd,
												Total_Controller.Yaw_Gyro_Control.Kp,
												Total_Controller.Yaw_Gyro_Control.Ki,
												Total_Controller.Yaw_Gyro_Control.Kd);
				ANO_Send_PID_Flag[0]=0;
		}
		
		else if(ANO_Cnt == 8 && ANO_Send_PID_Flag[1] == 1)//第2帧 PID
		{
				ANO_DT_Send_PID(2,Total_Controller.Roll_Angle_Control.Kp,
												Total_Controller.Roll_Angle_Control.Ki,
												Total_Controller.Roll_Angle_Control.Kd,
												Total_Controller.Pitch_Angle_Control.Kp,
												Total_Controller.Pitch_Angle_Control.Ki,
												Total_Controller.Pitch_Angle_Control.Kd,
												Total_Controller.Yaw_Angle_Control.Kp,
												Total_Controller.Yaw_Angle_Control.Ki,
												Total_Controller.Yaw_Angle_Control.Kd);
				ANO_Send_PID_Flag[1]=0;
		}
		
		else if(ANO_Cnt == 9 && ANO_Send_PID_Flag[2] == 1)//第3帧 PID
		{
				ANO_DT_Send_PID(3,Total_Controller.High_Speed_Control.Kp,
												Total_Controller.High_Speed_Control.Ki,
												Total_Controller.High_Speed_Control.Kd,
												Total_Controller.High_Position_Control.Kp,
												Total_Controller.High_Position_Control.Ki,
												Total_Controller.High_Position_Control.Kd,
												0,
												0,
												0);
				ANO_Send_PID_Flag[2]=0;
		}
		
		else if(ANO_Cnt == 10 && ANO_Send_PID_Flag[3] == 1)//第4帧 PID
		{
				ANO_DT_Send_PID(4,
												0,
												0,
												0,
												0,
												0,
												0,
												0,
												0,
												0);
				ANO_Send_PID_Flag[3]=0;
		}
		
		else if(ANO_Cnt == 11 && ANO_Send_PID_Flag[4] == 1)//第5帧 PID
		{
				ANO_DT_Send_PID(5,
												0,
												0,
												0,
												0,		
												0,
												0,				
												0,					
												0,						
												0);
				ANO_Send_PID_Flag[4]=0;
		}
		else if(ANO_Cnt == 12 && ANO_Send_PID_Flag[5] == 1)//第6帧 PID PropellerDir
		{
				ANO_DT_Send_PID(6,  
												0,
												0,
												0,
												0,
												0,
												0,
												0,
												0,
												0);
				ANO_Send_PID_Flag[5]=0;
				ANO_Cnt=0;
				Buzzer_Set(&Beep,1,1);
				//log_v("PID_Flash_Read -> success!");
		}					
}





//---------------这里是分隔符↓↓↓↓↓↓↓↓↓↓<以下为发送 函数>↓↓↓↓↓↓↓↓↓↓这里是分隔符------------------//

void Save_Or_Reset_PID_Parameter(void) 
{
		if(Sort_PID_Flag == 1)//将地面站设置PID参数写入Flash
		{
				PID_Parameter[0].p=Total_Controller.Roll_Gyro_Control.Kp;
				PID_Parameter[0].i=Total_Controller.Roll_Gyro_Control.Ki;
				PID_Parameter[0].d=Total_Controller.Roll_Gyro_Control.Kd;
			
				PID_Parameter[1].p=Total_Controller.Pitch_Gyro_Control.Kp;
				PID_Parameter[1].i=Total_Controller.Pitch_Gyro_Control.Ki;
				PID_Parameter[1].d=Total_Controller.Pitch_Gyro_Control.Kd;
				
				PID_Parameter[2].p=Total_Controller.Yaw_Gyro_Control.Kp;
				PID_Parameter[2].i=Total_Controller.Yaw_Gyro_Control.Ki;
				PID_Parameter[2].d=Total_Controller.Yaw_Gyro_Control.Kd;
				
				PID_Parameter[3].p=Total_Controller.Roll_Angle_Control.Kp;
				PID_Parameter[3].i=Total_Controller.Roll_Angle_Control.Ki;
				PID_Parameter[3].d=Total_Controller.Roll_Angle_Control.Kd;
			
				PID_Parameter[4].p=Total_Controller.Pitch_Angle_Control.Kp;
				PID_Parameter[4].i=Total_Controller.Pitch_Angle_Control.Ki;
				PID_Parameter[4].d=Total_Controller.Pitch_Angle_Control.Kd;
				
				PID_Parameter[5].p=Total_Controller.Yaw_Angle_Control.Kp;
				PID_Parameter[5].i=Total_Controller.Yaw_Angle_Control.Ki;
				PID_Parameter[5].d=Total_Controller.Yaw_Angle_Control.Kd;
				
				PID_Parameter[6].p=Total_Controller.High_Speed_Control.Kp;
				PID_Parameter[6].i=Total_Controller.High_Speed_Control.Ki;
				PID_Parameter[6].d=Total_Controller.High_Speed_Control.Kd;
				
				PID_Parameter[7].p=Total_Controller.High_Position_Control.Kp;
				PID_Parameter[7].i=Total_Controller.High_Position_Control.Ki;
				PID_Parameter[7].d=Total_Controller.High_Position_Control.Kd;			
			

			
				
				//log_v("PID_Save_Flash -> Success!");
				Save_PID_Parameter(); //保存参数至FLASH
				Buzzer_Set(&Beep,1,1);
				Sort_PID_Flag=0;
		}
		else if(Sort_PID_Flag==2)//将复位PID参数，并写入Flash
		{
			
				Total_PID_Init();//将PID参数重置为参数Control_Unit表里面参数
						
				PID_Parameter[0].p=Total_Controller.Roll_Gyro_Control.Kp;
				PID_Parameter[0].i=Total_Controller.Roll_Gyro_Control.Ki;
				PID_Parameter[0].d=Total_Controller.Roll_Gyro_Control.Kd;
			
				PID_Parameter[1].p=Total_Controller.Pitch_Gyro_Control.Kp;
				PID_Parameter[1].i=Total_Controller.Pitch_Gyro_Control.Ki;
				PID_Parameter[1].d=Total_Controller.Pitch_Gyro_Control.Kd;
				
				PID_Parameter[2].p=Total_Controller.Yaw_Gyro_Control.Kp;
				PID_Parameter[2].i=Total_Controller.Yaw_Gyro_Control.Ki;
				PID_Parameter[2].d=Total_Controller.Yaw_Gyro_Control.Kd;
				
				PID_Parameter[3].p=Total_Controller.Roll_Angle_Control.Kp;
				PID_Parameter[3].i=Total_Controller.Roll_Angle_Control.Ki;
				PID_Parameter[3].d=Total_Controller.Roll_Angle_Control.Kd;
			
				PID_Parameter[4].p=Total_Controller.Pitch_Angle_Control.Kp;
				PID_Parameter[4].i=Total_Controller.Pitch_Angle_Control.Ki;
				PID_Parameter[4].d=Total_Controller.Pitch_Angle_Control.Kd;
				
				PID_Parameter[5].p=Total_Controller.Yaw_Angle_Control.Kp;
				PID_Parameter[5].i=Total_Controller.Yaw_Angle_Control.Ki;
				PID_Parameter[5].d=Total_Controller.Yaw_Angle_Control.Kd;
				
				PID_Parameter[6].p=Total_Controller.High_Speed_Control.Kp;
				PID_Parameter[6].i=Total_Controller.High_Speed_Control.Ki;
				PID_Parameter[6].d=Total_Controller.High_Speed_Control.Kd;
				
				PID_Parameter[7].p=Total_Controller.High_Position_Control.Kp;
				PID_Parameter[7].i=Total_Controller.High_Position_Control.Ki;
				PID_Parameter[7].d=Total_Controller.High_Position_Control.Kd;
				

				Save_PID_Parameter(); //保存参数至FLASH
				
				Sort_PID_Flag = 0;
				Buzzer_Set(&Beep,1,1);
				//log_v("PID_Reset_Flash -> Success!");
				ANO_Send_PID_Flag[0]=1;//回复默认参数后，将更新的数据发送置地面站		
				ANO_Send_PID_Flag[1]=1;
				ANO_Send_PID_Flag[2]=1;
				ANO_Send_PID_Flag[3]=1;
				ANO_Send_PID_Flag[4]=1;
				ANO_Send_PID_Flag[5]=1;
		}
	
		else {
				return;
		}
}
