zengwangfa/2019-Electronic-Design-Competition/others/software for rail gun/rt-thread-master/bsp/stm32f40x/applications/flash.c

/*
 * flash.c
 *
 *  Created on: 2019年2月30日
 *      Author: zengwangfa
 *      Notes:  Flash读写方法
 */
#define LOG_TAG       "flash"


#include <math.h>
#include <easyflash.h>
#include <rtthread.h>
#include <elog.h>

#include "oled.h"
#include "Control.h"
#include "PID.h"
#include "debug.h"
#include "flash.h"
#include "sensor.h"
#include "drv_ano.h"
#include "servo.h"
#include "propeller.h"
#include "PropellerControl.h"
#include "gyroscope.h"
#include "EasyThread.h"

/*---------------------- Constant / Macro Definitions -----------------------*/

//FLASH起始地址   W25Q128 16M 的容量分为 256 个块（Block）
#define Nor_FLASH_ADDRESS    (0x0000) 	//W25Q128 FLASH的 普通起始地址   【第个扇区】

#define IMP_FLASH_ADDRESS    (0x1000) 	//W25Q128 FLASH的 重要参数起始地址 【第个扇区】

/*----------------------- Variable Declarations -----------------------------*/

int16 PowerPercent = 0;
int Extractor_Value = 0;

PID_Parameter_Flag  PID_Parameter_Read_Flag;

uint32 Normal_Parameter[PARAMEMER_MAX_NUMBER_e]={0};

/*----------------------- Function Implement --------------------------------*/

int flash_thread_init(void)
{
    rt_thread_t flash_tid;
		/*创建动态线程*/
    flash_tid = rt_thread_create("flash",//线程名称
                    flash_thread_entry,				 //线程入口函数【entry】
                    RT_NULL,							   //线程入口函数参数【parameter】
                    1024,										 //线程栈大小，单位是字节【byte】
                    15,										 	 //线程优先级【priority】
                    10);										 //线程的时间片大小【tick】= 100ms

    if (flash_tid != RT_NULL){

				rt_thread_startup(flash_tid);
		}
		return 0;
}
INIT_APP_EXPORT(flash_thread_init);


/*******************************************
* 函 数 名：Normal_Parameter_Init_With_Flash
* 功    能：读取Flash普通参数【非常重要】
* 输入参数：none
* 返 回 值：none
* 注    意：NORMAL_PARAMETER_TABLE 枚举表 中添加自身需要的的参数的 枚举值
						NORMAL_PARAMETER_TABLE 枚举表 中添加自身需要的的参数

********************************************/
int Normal_Parameter_Init_With_Flash(void)
{
		uint8 i = 0;
		for(i = 0;i < PARAMEMER_MAX_NUMBER_e;i++ ){
				ef_port_read(Nor_FLASH_ADDRESS+4*i,(Normal_Parameter+i),4);		 //Flash读取
		}
		Normal_Parameter_SelfCheck_With_Flash();//Flash参数自检 若为 0 则为 非正常数据，则不传递给真实数据 

		log_i("Flash_Read()");
//		log_i("                      ----------");
//		log_i("VehicleMode           |%s  |",VehicleModeName[VehicleMode]);
//		log_i("WorkMode              |%s    |",WorkModeName[WorkMode]);
//		log_i("Depth Sensor Type     |%s  |",Depth_Sensor_Name[Sensor.DepthSensor.Type]); //深度传感器类型
//		log_i("debug_tool            |%s     |",debug_tool_name[debug_tool]);
//		log_i("                      ----------");
		return 0;
}


void Normal_Parameter_SelfCheck_With_Flash(void) //Flash参数自检 若为 0 则为 非正常数据 
{
		Parameter_SelfCheck( (uint32 *)&VehicleMode,&Normal_Parameter[VEHICLE_MODE_e] );//航行器模式  rov/auv
		Parameter_SelfCheck( (uint32 *)&debug_tool, &Normal_Parameter[DEBUG_TOOL_e] );   //debug工具  vcan/ano
		
		Parameter_SelfCheck( (uint32 *)&RoboticArm.MaxValue,&Normal_Parameter[ROBOTIC_ARM_MAX_VALUE_e] );//机械臂参数
		Parameter_SelfCheck( (uint32 *)&RoboticArm.MinValue,&Normal_Parameter[ROBOTIC_ARM_MIN_VALUE_e] );
		Parameter_SelfCheck( (uint32 *)&RoboticArm.MedValue,&Normal_Parameter[ROBOTIC_ARM_MED_VALUE_e] );
		Parameter_SelfCheck( (uint32 *)&RoboticArm.Speed   ,&Normal_Parameter[ROBOTIC_ARM_SPEED_e] );	
	
		Parameter_SelfCheck( (uint32 *)&YunTai.MaxValue,&Normal_Parameter[YUNTAI_MAX_VALUE_e] );//云台参数
		Parameter_SelfCheck( (uint32 *)&YunTai.MinValue,&Normal_Parameter[YUNTAI_MIN_VALUE_e] );	
		Parameter_SelfCheck( (uint32 *)&YunTai.MedValue,&Normal_Parameter[YUNTAI_MED_VALUE_e] );  
		Parameter_SelfCheck( (uint32 *)&YunTai.Speed   ,&Normal_Parameter[YUNTAI_SPEED_e] );	
	
		Parameter_SelfCheck( (uint32 *)&Compass_Offset_Angle,&Normal_Parameter[COMPASS_OFFSET_ANGLE_e] );//指南针补偿角度

		/* 【推进器方向】 */
		Parameter_SelfCheck( (uint32 *)&PropellerDir.rightUp    ,&Normal_Parameter[PROPELLER_RIGHT_UP_DIR_e]  );// 右上  【推进器方向 参数】
		Parameter_SelfCheck( (uint32 *)&PropellerDir.leftDown   ,&Normal_Parameter[PROPELLER_LEFT_DOWN_DIR_e] );// 左下  【推进器方向 参数】	
		Parameter_SelfCheck( (uint32 *)&PropellerDir.leftUp     ,&Normal_Parameter[PROPELLER_LEFT_UP_DIR_e]   );// 左上  【推进器方向 参数】	
		Parameter_SelfCheck( (uint32 *)&PropellerDir.rightDown  ,&Normal_Parameter[PROPELLER_RIGHT_DOWN_DIR_e]);// 右下  【推进器方向 参数】
		Parameter_SelfCheck( (uint32 *)&PropellerDir.leftMiddle ,&Normal_Parameter[PROPELLER_LEFT_MED_DIR_e]  );// 左中  【推进器方向 参数】
		Parameter_SelfCheck( (uint32 *)&PropellerDir.rightMiddle,&Normal_Parameter[PROPELLER_RIGHT_MED_DIR_e] );// 右中  【推进器方向 参数】	

		/* 【推进器动力系数】  */
		Parameter_SelfCheck( (uint32 *)&PowerPercent,&Normal_Parameter[PROPELLER_POWER_e] );// 右中  【推进器方向 参数】	
				
		/* 【深度传感器类型】  */
		Parameter_SelfCheck( (uint32 *)&Sensor.DepthSensor.Type,&Normal_Parameter[DEPTH_SENSOR_TYPE_e] );//深度传感器 MS5837/SPL1301
		
		/* 【电池容量类型】  */
		Parameter_SelfCheck( (uint32 *)&Sensor.PowerSource.Capacity,&Normal_Parameter[BATTERY_CAPACITY_e] );//电池容量参数 3s/4s/6s
		
		/* 【吸取器吸力】  */
		Parameter_SelfCheck( (uint32 *)&Extractor_Value,&Normal_Parameter[EXTRACTOR_VALUE_e] );//吸取器吸力
		
		/* 【吸取器吸力】  */
		Parameter_SelfCheck( (uint32 *)&WorkMode,&Normal_Parameter[WORK_MODE_e] );//

		/* 【推进器偏差值】*/
		Parameter_SelfCheck( (uint32 *)&PropellerError.leftUp,&Normal_Parameter[PROPELLER_RIGHT_UP_ERROR_e] );
		Parameter_SelfCheck( (uint32 *)&PropellerError.leftDown,&Normal_Parameter[PROPELLER_LEFT_DOWN_ERROR_e] );
		Parameter_SelfCheck( (uint32 *)&PropellerError.leftUp,&Normal_Parameter[PROPELLER_LEFT_UP_ERROR_e] );
		Parameter_SelfCheck( (uint32 *)&PropellerError.rightDown,&Normal_Parameter[PROPELLER_RIGHT_DOWN_ERROR_e] );
		Parameter_SelfCheck( (uint32 *)&PropellerError.leftMiddle,&Normal_Parameter[PROPELLER_LEFT_MED_ERROR_e] );
		Parameter_SelfCheck( (uint32 *)&PropellerError.rightMiddle,&Normal_Parameter[PROPELLER_RIGHT_MED_ERROR_e] );
}
/*
void test_env(void) {
    uint32_t i_boot_times = NULL;
    char *c_old_boot_times, c_new_boot_times[11] = {0};

    // get the boot count number from Env 
    c_old_boot_times = ef_get_env("boot_times");
    RT_ASSERT(c_old_boot_times);
    i_boot_times = atol(c_old_boot_times);//atoi
    // boot count +1 
    i_boot_times ++;
    rt_kprintf("The system now boot %d times\n", i_boot_times);
    // interger to string 
    sprintf(c_new_boot_times,"%ld", i_boot_times);
    // set and store the boot count number to Env 
    ef_set_env("boot_times", c_new_boot_times);
    ef_save_env();
}
*/
/* FLASH 更新 普通参数 */
void Flash_Update(void)
{
		ef_port_erase(Nor_FLASH_ADDRESS,4);	//【普通参数FLASH】先擦后写  擦除的为一个扇区4096 Byte 
//------------------------------------------------------------------------------------------//
		ef_port_write(Nor_FLASH_ADDRESS+4*VEHICLE_MODE_e,(uint32 *)(&VehicleMode),4);		
		ef_port_write(Nor_FLASH_ADDRESS+4*DEBUG_TOOL_e,(uint32 *)(&debug_tool),4);		  

		ef_port_write(Nor_FLASH_ADDRESS+4*ROBOTIC_ARM_MAX_VALUE_e,(uint32 *)&RoboticArm.MaxValue,4);		// 地址
		ef_port_write(Nor_FLASH_ADDRESS+4*ROBOTIC_ARM_MIN_VALUE_e,(uint32 *)&RoboticArm.MinValue,4); // 地址
		ef_port_write(Nor_FLASH_ADDRESS+4*ROBOTIC_ARM_MED_VALUE_e,(uint32 *)&RoboticArm.MedValue,4); // 地址
		ef_port_write(Nor_FLASH_ADDRESS+4*ROBOTIC_ARM_SPEED_e,(uint32 *)&RoboticArm.Speed,4); // 地址
	
	
		ef_port_write(Nor_FLASH_ADDRESS+4*YUNTAI_MAX_VALUE_e,(uint32 *)&YunTai.MaxValue,4); //云台最大值
		ef_port_write(Nor_FLASH_ADDRESS+4*YUNTAI_MIN_VALUE_e,(uint32 *)&YunTai.MinValue,4); 
		ef_port_write(Nor_FLASH_ADDRESS+4*YUNTAI_MED_VALUE_e,(uint32 *)&YunTai.MedValue,4); // 云台中值
		ef_port_write(Nor_FLASH_ADDRESS+4*YUNTAI_SPEED_e,(uint32 *)&YunTai.Speed,4); 

		ef_port_write(Nor_FLASH_ADDRESS+4*COMPASS_OFFSET_ANGLE_e,(uint32 *)&Compass_Offset_Angle,4); // 地址

		ef_port_write(Nor_FLASH_ADDRESS+4*PROPELLER_RIGHT_UP_DIR_e  ,(uint32 *)&PropellerDir.rightUp    ,4); //右上
		ef_port_write(Nor_FLASH_ADDRESS+4*PROPELLER_LEFT_DOWN_DIR_e ,(uint32 *)&PropellerDir.leftDown   ,4); //左下
		ef_port_write(Nor_FLASH_ADDRESS+4*PROPELLER_LEFT_UP_DIR_e   ,(uint32 *)&PropellerDir.leftUp     ,4); //左上
		ef_port_write(Nor_FLASH_ADDRESS+4*PROPELLER_RIGHT_DOWN_DIR_e,(uint32 *)&PropellerDir.rightDown  ,4); //右下
		ef_port_write(Nor_FLASH_ADDRESS+4*PROPELLER_LEFT_MED_DIR_e  ,(uint32 *)&PropellerDir.leftMiddle ,4); //左中
		ef_port_write(Nor_FLASH_ADDRESS+4*PROPELLER_RIGHT_MED_DIR_e ,(uint32 *)&PropellerDir.rightMiddle,4); //右中

		ef_port_write(Nor_FLASH_ADDRESS+4*PROPELLER_POWER_e ,(uint32 *)&PowerPercent,4); //推进器动力百分比
		
		ef_port_write(Nor_FLASH_ADDRESS+4*DEPTH_SENSOR_TYPE_e ,(uint32 *)&Sensor.DepthSensor.Type,4); //深度传感器 类型
		
		ef_port_write(Nor_FLASH_ADDRESS+4*BATTERY_CAPACITY_e ,(uint32 *)&Sensor.PowerSource.Capacity,4); //电池容量参数 3s/4s/6s
		
		ef_port_write(Nor_FLASH_ADDRESS+4*EXTRACTOR_VALUE_e ,(uint32 *)&Extractor_Value,4); //吸取器吸力

		ef_port_write(Nor_FLASH_ADDRESS+4*WORK_MODE_e ,(uint32 *)&WorkMode,4); //工作模式
		
		ef_port_write(Nor_FLASH_ADDRESS+4*PROPELLER_RIGHT_UP_ERROR_e   ,(uint32 *)&PropellerError.rightUp,4); //
		ef_port_write(Nor_FLASH_ADDRESS+4*PROPELLER_LEFT_DOWN_ERROR_e  ,(uint32 *)&PropellerError.leftDown,4); //
		ef_port_write(Nor_FLASH_ADDRESS+4*PROPELLER_LEFT_UP_ERROR_e    ,(uint32 *)&PropellerError.leftUp,4); //
		ef_port_write(Nor_FLASH_ADDRESS+4*PROPELLER_RIGHT_DOWN_ERROR_e ,(uint32 *)&PropellerError.rightDown,4); //
		ef_port_write(Nor_FLASH_ADDRESS+4*PROPELLER_LEFT_MED_ERROR_e   ,(uint32 *)&PropellerError.leftMiddle,4); //
		ef_port_write(Nor_FLASH_ADDRESS+4*PROPELLER_RIGHT_MED_ERROR_e  ,(uint32 *)&PropellerError.rightMiddle,4); //
}	
MSH_CMD_EXPORT(Flash_Update,Flash Update);

/* list 相关重要参数 */
void list_value(void)
{

		log_i	("variable  name          value");
    log_i("----------------------   ---------");

		log_i("VehicleMode               %s",VehicleModeName[VehicleMode]);
		log_i("WorkMode                  %s",WorkModeName[WorkMode]);
		log_i("Depth Sensor Type         %s",Depth_Sensor_Name[Sensor.DepthSensor.Type]); //深度传感器类型
		log_i("debug_tool                %s",debug_tool_name[debug_tool]);
	  log_i("----------------------   ---------");
	  log_i("RoboticArm.MaxValue       %d",RoboticArm.MaxValue);
	  log_i("RoboticArm.MinValue       %d",RoboticArm.MinValue);
		log_i("RoboticArm.CurrentValue   %d",RoboticArm.CurrentValue);
		log_i("RoboticArm.Speed          %d",RoboticArm.Speed);
	  log_i("----------------------   ---------");
	  log_i("YunTai.MaxValue           %d",YunTai.MaxValue);
		log_i("YunTai.MedValue           %d",YunTai.MedValue);
	  log_i("YunTai.MinValue           %d",YunTai.MinValue);
		log_i("YunTai.CurrentValue       %d",YunTai.CurrentValue);
		log_i("YunTai.Speed              %d",YunTai.Speed);
	  log_i("----------------------   ---------");
	  log_i("Propeller_Max             %d",PropellerParameter.PowerMax);
		log_i("Propeller_Med             %d",PropellerParameter.PowerMed);
	  log_i("Propeller_Min             %d",PropellerParameter.PowerMin);
		log_i("----------------------   ---------");
		log_i("Compass Offset Angle      %d",Compass_Offset_Angle);//指南针 偏移角度
		log_i("----------------------   ---------");
		log_i("Propeller_Power           %d",PowerPercent);//推进器动力百分比【不用，动力百分比由控制字给的】
		log_i("----------------------   ---------");
		log_i("Battery Capacity          %0.3f",Sensor.PowerSource.Capacity);//电池容量参数
		log_i("----------------------   ---------");
		log_i("Extractor_Value           %d",Extractor_Value);//吸取器动力值	
		log_i("----------------------   ---------");		

		
    rt_kprintf("\n");
}
MSH_CMD_EXPORT(list_value,list some important values);



void Save_PID_Parameter(void)//保存PID参数
{
		uint8 i = 0;
		
		ef_port_erase(IMP_FLASH_ADDRESS,4);	//【重要参数FLASH】先擦后写  擦除的为一个扇区4096 Byte
		for(i = 0;i < PID_USE_NUM;i++){
				ef_port_write(IMP_FLASH_ADDRESS+12*(PID1_PARAMETER_KP+i*3)+0,(uint32 *)&PID_Parameter[i].p,4);//第i+1组PID
				ef_port_write(IMP_FLASH_ADDRESS+12*(PID1_PARAMETER_KP+i*3)+4,(uint32 *)&PID_Parameter[i].i,4);
				ef_port_write(IMP_FLASH_ADDRESS+12*(PID1_PARAMETER_KP+i*3)+8,(uint32 *)&PID_Parameter[i].d,4);
			
		}

}

int PID_Paramter_Init_With_Flash(void)//初始化读取PID参数
{
		uint8 i = 0;
		Total_PID_Init();//初始化PID参数表
		for(i = 0;i < PID_USE_NUM;i++){
				ef_port_read(IMP_FLASH_ADDRESS+12*(PID1_PARAMETER_KP+i*3)+0,(uint32 *)&PID_Parameter[i].p,4);//第i+1组PID
				ef_port_read(IMP_FLASH_ADDRESS+12*(PID1_PARAMETER_KP+i*3)+4,(uint32 *)&PID_Parameter[i].i,4);
				ef_port_read(IMP_FLASH_ADDRESS+12*(PID1_PARAMETER_KP+i*3)+8,(uint32 *)&PID_Parameter[i].d,4);
			
				if(isnan(PID_Parameter[i].p)==0
						&&isnan(PID_Parameter[i].i)==0
							&&isnan(PID_Parameter[i].d)==0){ //判断数据是否isnan(not a number无效数字)
						PID_Parameter_Read_Flag.No_0xFF[i]=0x01;
				 }
			
		}

		
		if(PID_Parameter_Read_Flag.No_0xFF[0]!=0x00
			 &&PID_Parameter_Read_Flag.No_0xFF[1]!=0x00
				 &&PID_Parameter_Read_Flag.No_0xFF[2]!=0x00
					 &&PID_Parameter_Read_Flag.No_0xFF[3]!=0x00
						 &&PID_Parameter_Read_Flag.No_0xFF[4]!=0x00
							 &&PID_Parameter_Read_Flag.No_0xFF[5]!=0x00
								 &&PID_Parameter_Read_Flag.No_0xFF[6]!=0x00
									 &&PID_Parameter_Read_Flag.No_0xFF[7]!=0x00)//Flash内数据正常，更新PID参数值
		{
				Total_Controller.Roll_Gyro_Control.Kp=PID_Parameter[0].p;
				Total_Controller.Roll_Gyro_Control.Ki=PID_Parameter[0].i;
				Total_Controller.Roll_Gyro_Control.Kd=PID_Parameter[0].d;
		
				Total_Controller.Pitch_Gyro_Control.Kp=PID_Parameter[1].p;
				Total_Controller.Pitch_Gyro_Control.Ki=PID_Parameter[1].i;
				Total_Controller.Pitch_Gyro_Control.Kd=PID_Parameter[1].d;
					
				Total_Controller.Yaw_Gyro_Control.Kp=PID_Parameter[2].p;
				Total_Controller.Yaw_Gyro_Control.Ki=PID_Parameter[2].i;
				Total_Controller.Yaw_Gyro_Control.Kd=PID_Parameter[2].d;
						
				Total_Controller.Roll_Angle_Control.Kp=PID_Parameter[3].p;
				Total_Controller.Roll_Angle_Control.Ki=PID_Parameter[3].i;
				Total_Controller.Roll_Angle_Control.Kd=PID_Parameter[3].d;
				
				Total_Controller.Pitch_Angle_Control.Kp=PID_Parameter[4].p;
				Total_Controller.Pitch_Angle_Control.Ki=PID_Parameter[4].i;
				Total_Controller.Pitch_Angle_Control.Kd=PID_Parameter[4].d;

				Total_Controller.Yaw_Angle_Control.Kp=PID_Parameter[5].p;
				Total_Controller.Yaw_Angle_Control.Ki=PID_Parameter[5].i;
				Total_Controller.Yaw_Angle_Control.Kd=PID_Parameter[5].d;
				
				Total_Controller.High_Speed_Control.Kp=PID_Parameter[6].p;
				Total_Controller.High_Speed_Control.Ki=PID_Parameter[6].i;
				Total_Controller.High_Speed_Control.Kd=PID_Parameter[6].d;
				
				Total_Controller.High_Position_Control.Kp=PID_Parameter[7].p;
				Total_Controller.High_Position_Control.Ki=PID_Parameter[7].i;
				Total_Controller.High_Position_Control.Kd=PID_Parameter[7].d;

				
				
		}
		return 0;
}
INIT_APP_EXPORT(PID_Paramter_Init_With_Flash);



void Parameter_SelfCheck(uint32 *RealParameter,uint32 *TempParameter)
{
		//int isnan(x)函数 当x时nan返回1，其它返回0
		if( isnan(*TempParameter) == 0 ) {//如果不是无效数字 not a number,则判定为正确
				*RealParameter = *TempParameter; //Flash 数据正确则替换为真实变量
		}
}
