zengwangfa/2019-Electronic-Design-Competition/others/software for development board/rt-thread-master/bsp/stm32f40x/applications/oledfont.h

#ifndef __OLEDFONT_H_
#define __OLEDFONT_H_ 

//常用ASCII表
//偏移量32 
//ASCII字符集: !"#$%&'()*+,-./0123456789:;<=>?@ABCDEFGHIJKLMNOPQRSTUVWXYZ[\]^_`abcdefghijklmnopqrstuvwxyz{|}~
//PC2LCD2002取模方式设置：阴码+逐列式+顺向+C51格式
//总共：3个字符集（12*12、16*16和24*24），用户可以自行新增其他分辨率的字符集。
//每个字符所占用的字节数为:(size/8+((size%8)?1:0))*(size/2),其中size:是字库生成时的点阵大小(12/16/24...)


/*  PC2LCD2002取模方式设置：阴码+逐列式+顺向+C51格式  */
static const unsigned char my_font_1206[2][32]={	

//{0x06,0x00,0x0E,0x00,0x1C,0x00,0x38,0x40,0x30,0xC0,0x71,0x80,0x73,0x00,0x73,0x18},
//{0x73,0x18,0x73,0x00,0x71,0x80,0x38,0xC0,0x38,0x40,0x1C,0x00,0x0E,0x00,0x06,0x00},/*"C:\Users\zengwangfa\Desktop\wifi.bmp",0*/
///* (16 X 16 ) */
{0x00,0x00,0xF0,0x10,0x10,0x10,0x10,0xFF,0x10,0x10,0x10,0x10,0xF0,0x00,0x00,0x00},
{0x00,0x00,0x0F,0x04,0x04,0x04,0x04,0xFF,0x04,0x04,0x04,0x04,0x0F,0x00,0x00,0x00},/*"中",0*/

	 
};
static const unsigned char my_font_1608[8][16]={	
	


{0x04,0x00,0x0C,0x00,0x1F,0xF8,0x00,0x00,0x00,0x00,0x1F,0xF8,0x00,0x30,0x00,0x20},/*"3G",0*/
/* (8 X 16 ) */

{0x08,0x00,0x19,0x00,0x13,0x00,0x12,0x60,0x12,0x60,0x13,0x00,0x19,0x00,0x08,0x00},/*"WIFI",1*/
/* (8 X 16 ) */

{0x00,0x00,0x00,0x00,0x00,0x00,0x00,0x00,0x00,0x00,0x00,0x00,0x00,0x00,0x00,0x00},/*" ",2*/

};
//12*12 ASCII字符集点阵
static const unsigned char asc2_1206[95][12]={
{0x00,0x00,0x00,0x00,0x00,0x00,0x00,0x00,0x00,0x00,0x00,0x00},/*" ",0*/
{0x00,0x00,0x00,0x00,0x3F,0x40,0x00,0x00,0x00,0x00,0x00,0x00},/*"!",1*/
{0x00,0x00,0x30,0x00,0x40,0x00,0x30,0x00,0x40,0x00,0x00,0x00},/*""",2*/
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
		0x12,0x02,0xFE,0x02,0x13,0xF2,0x12,0x0A,0x12,0x0A,0x02,0x3A,0x00,0x02,0x00,0x00},/*"选",39*/
		{0x08,0x42,0x08,0x41,0xFF,0xFE,0x08,0x80,0x00,0x00,0x41,0x08,0x61,0x48,0x52,0x48,
		0x4A,0x48,0x45,0xFF,0x4A,0x48,0x52,0x48,0x61,0x48,0x01,0x08,0x01,0x00,0x00,0x00},/*"择",40*/
};

#endif
