zengwangfa/2019-Electronic-Design-Competition/others/software for rail gun/rt-thread-master/bsp/stm32f40x/applications/ioDevices.c

/*
 * key.c
 *
 *  Created on: 2019年2月30日
 *      Author: zengwangfa
 *      Notes:  IO 设备控制（KEY、BUZZER）
 */


#define LOG_TAG  "ioDevices"//Tag

#include <drivers/pin.h>
#include <elog.h>
#include "ioDevices.h"
#include "oled.h"
#include "EasyThread.h"
/*---------------------- Constant / Macro Definitions -----------------------*/
#define KEY_PIN  						88 	 //PDG3   按键IO

#define WIFI_CONNECT_PIN    80 	 //PD11   WIFI连接IO检测
#define WIFI_RELOAD_PIN     68 	 //PE15   WIFI复位IO

#define BOMA3_PIN 					13	 //PF3   拨码开关IO
#define BOMA2_PIN	  				15	 //PF5
#define BOMA1_PIN 					14	 //PF4  

#define Buzzer_PIN 					59   //PE8   蜂鸣器IO

#define boma1_read 					rt_pin_read(BOMA1_PIN)
#define boma2_read 					rt_pin_read(BOMA2_PIN)
#define boma3_read 					rt_pin_read(BOMA3_PIN)

#define wifi_read 					rt_pin_read(WIFI_CONNECT_PIN)


#define Rail_GUN_PIN1     67

#define Rail_GUN_PIN2     60




/*----------------------- Variable Declarations -----------------------------*/
/* ALL_init 事件控制块. */
extern struct rt_event init_event;

Buzzer_Type Beep;  //蜂鸣器控制器


/*----------------------- Function Implement --------------------------------*/


int ioDevices_thread_init(void)
{
   rt_thread_t ioDecices_tid;

    ioDecices_tid = rt_thread_create("ioDev",ioDevices_thread_entry, RT_NULL,512,25, 10);

    if (ioDecices_tid != RT_NULL){			
				rt_pin_mode(KEY_PIN , PIN_MODE_INPUT_PULLUP);    //功能按键、拨码开关  上拉输入
				rt_pin_mode(BOMA1_PIN, PIN_MODE_INPUT_PULLUP);  //拨码开关  上拉输入
				rt_pin_mode(BOMA2_PIN, PIN_MODE_INPUT_PULLUP);  
				rt_pin_mode(BOMA3_PIN, PIN_MODE_INPUT_PULLUP);  
	
				rt_pin_mode(WIFI_RELOAD_PIN, PIN_MODE_OUTPUT);  //WIFI 连接IO检测
				rt_pin_write(WIFI_RELOAD_PIN ,PIN_HIGH);
			
				rt_pin_mode(Rail_GUN_PIN1, PIN_MODE_OUTPUT);  //WIFI 连接IO检测
				rt_pin_write(Rail_GUN_PIN1 ,PIN_LOW);
				rt_pin_mode(Rail_GUN_PIN2, PIN_MODE_OUTPUT);  //WIFI 连接IO检测
				rt_pin_write(Rail_GUN_PIN2 ,PIN_LOW);

			
		
			
			
				rt_pin_mode (Buzzer_PIN, PIN_MODE_OUTPUT);  //输出模式
				rt_pin_write(Buzzer_PIN, PIN_LOW);
			
				rt_pin_attach_irq(KEY_PIN, PIN_IRQ_MODE_FALLING, key_down, RT_NULL);/* 绑定中断，上升沿模式，回调函数名为key_down */
				rt_pin_irq_enable(KEY_PIN, PIN_IRQ_ENABLE);/* 使能中断 */
			
				log_i("IoDev_Init()");
				rt_thread_startup(ioDecices_tid);
		}
		return 0;
}
INIT_APP_EXPORT(ioDevices_thread_init);


void rail_gun_start_charge(void)
	{

		rt_pin_write(Rail_GUN_PIN2 ,PIN_HIGH);
		rt_thread_mdelay(10000);
	
		rt_pin_write(Rail_GUN_PIN2 ,PIN_LOW);

}

void rail_gun_start_up(void)
	{

		rt_pin_write(Rail_GUN_PIN1 ,PIN_HIGH);
		rt_thread_mdelay(500);
	
		rt_pin_write(Rail_GUN_PIN1 ,PIN_LOW);

}


/* get 2位拨码值 */
uint8 get_boma_value(void)
{
    static uint8 val = 0; //reserve(存储)
    
		val = boma1_read *1 + boma2_read *2 + boma3_read *4 + 1; //得到8种状态(1~8)
    return val;
}

/**
	* @brief  is_wifi_connect(wifi是否连接)
  * @param  None
  * @retval 1 连接上   0无连接
  * @notice 
  */
uint8 is_wifi_connect(void)
{
		return !wifi_read; 
}

/* 按键按下产生的任务 */
void key_down(void *args)  
{
				oled.pagenum ++;				
}



/*buzzer为蜂鸣器控制器  count为响的次数  length响的时间长度  */
void Buzzer_Set(Buzzer_Type* buzzer,uint8_t count,uint8_t length)
{
		buzzer->count  = count *2;	//响与不向为 两次状态，所以 *2
		buzzer->time   = length*5; //保存时间间隔长度
		buzzer->number = length*5; //计时间长度
}  

/* 蜂鸣器鸣响任务【可指示系统各个状态】 */
void Buzzer_Process(Buzzer_Type * buzzer)
{
		if(buzzer->count >= 1)//如果响的次数大于等于1
		{  
				if(buzzer->number >= 1){
						if(1 == buzzer->count%2)   {rt_pin_write(Buzzer_PIN, PIN_HIGH);}//【响一声】
						else                    	{rt_pin_write(Buzzer_PIN, PIN_LOW) ;} 
						buzzer->number--;	//时间间隔 减1
				}
				else{
						buzzer->number = buzzer->time;//响一次完成 后重新赋值
						buzzer->count--;  //次数减1
				}
		}
		else
		{
				rt_pin_write(Buzzer_PIN, PIN_LOW); //完成后拉低【不响】
				buzzer->time  = 0;
				buzzer->count = 0;
		}
}





/*【WIFI】重启MSH命令 */
int wifi_reload(void)
{
		rt_pin_write(WIFI_RELOAD_PIN ,PIN_LOW);
		rt_thread_mdelay(4000);
		rt_pin_write(WIFI_RELOAD_PIN ,PIN_HIGH);
		rt_thread_mdelay(1000);
		log_d("WIFI Reload!\r\n");
		return 0;

}
MSH_CMD_EXPORT(wifi_reload,wifi reload);
