zengwangfa/2019-Electronic-Design-Competition/others/software for development board/rt-thread-master/bsp/stm32f40x/applications/fuzzy.c

/*模糊优化p*/

#include <math.h>
#include "fuzzy.h"
#define PMAX    100
#define PMIN    -100
#define DMAX    100
#define DMIN    -100
#define FMAX    100       
/*语言值的满幅值*/


//PD当做上下极板的 滤波
  
/**********************************************************/
float Fuzzy(float *P,float *D)   /*模糊*/
{

float off_set = 5.0f; 
	
/*输入量P语言的特征点*/
float PFF[4]={0,8,16,24};//{0,12,24,48};
/*输入量D语言的特征点*/
float DFF[4]={0,5,10,15};//{0,16,32,64};

/*输出量U的语言值的特征点*/
float UFF[7]={2*off_set,3*off_set,4*off_set,5*off_set,6*off_set,7*off_set,8*off_set};//{0,15,30,45,60,75,90};

int rule[7][7]={ 
     //ec -3,-2,-1, 0, 1, 2, 3   //    e
      { 0, 0, 1, 1, 2, 2, 3,},   //   -3`
      { 0, 1, 1, 2, 2, 3, 4,},   //   -2
      { 1, 1, 2, 3, 4, 5, 6,},   //   -1
      { 1, 2, 3, 4, 5, 6, 6,},   //    0
      { 2, 3, 4, 5, 6, 6, 6,},   //    1
      { 3, 4, 5, 6, 6, 6, 6,},   //    2
      { 4, 5, 6, 6, 6, 6, 6 }    //    3
 };   
  



float    U;           
/*偏差,偏差微分以及输出值的精确量*/
int   PF[2],DF[2],UF[4];  
/*偏差,偏差微分以及输出值的隶属度*/
int    Pn,Dn,Un[4];
long   temp1,temp2;

/*隶属度的确定*/
/*根据P/偏差/D/偏差的变化量/的指定语言获得有效隶属度*/
if(*P>-PFF[3] && *P<PFF[3])
{
    if(*P<=-PFF[2])
	{
		 Pn=-2;
		 PF[0]=FMAX*((float)(-PFF[2]-*P)/(PFF[3]-PFF[2]));
	}
    else if(*P<=-PFF[1])
   {
    Pn=-1;
    PF[0]=FMAX*((float)(-PFF[1]-*P)/(PFF[2]-PFF[1]));
   }
    else if(*P<=PFF[0])
   {
    Pn=0;
    PF[0]=FMAX*((float)(-PFF[0]-*P)/(PFF[1]-PFF[0]));
   }
    else if(*P<=PFF[1])
   {
    Pn=1; PF[0]=FMAX*((float)(PFF[1]-*P)/(PFF[1]-PFF[0]));
   }
    else if(*P<=PFF[2])
   {
    Pn=2; PF[0]=FMAX*((float)(PFF[2]-*P)/(PFF[2]-PFF[1]));
   }
    else if(*P<=PFF[3])
   {
    Pn=3; PF[0]=FMAX*((float)(PFF[3]-*P)/(PFF[3]-PFF[2]));
   }
    }
else if(*P<=-PFF[3])
   {
    Pn=-2;   PF[0]=FMAX;
   }
else if(*P>=PFF[3])
   {
    Pn=3;   PF[0]=0;
   }
PF[1]=FMAX-PF[0];
if(*D>-DFF[3] && *D<DFF[3])
{
		if(*D<=-DFF[2])
		{
			 Dn=-2;DF[0]=FMAX*((float)(-DFF[2]-*D)/(DFF[3]-DFF[2]));
		}
    else if(*D<=-DFF[1])
   {
    Dn=-1;
    DF[0]=FMAX*((float)(-DFF[1]-*D)/(DFF[2]-DFF[1]));
   }
    else if(*D<=DFF[0])
   {
    Dn=0;
    DF[0]=FMAX*((float)(-DFF[0]-*D)/(DFF[1]-DFF[0]));
   }
    else if(*D<=DFF[1])
   {
    Dn=1;
    DF[0]=FMAX*((float)(DFF[1]-*D)/(DFF[1]-DFF[0]));
   }
    else if(*D<=DFF[2])
   {
    Dn=2; DF[0]=FMAX*((float)(DFF[2]-*D)/(DFF[2]-DFF[1]));
   }
    else if(*D<=DFF[3])
   {
    Dn=3; DF[0]=FMAX*((float)(DFF[3]-*D)/(DFF[3]-DFF[2]));
   }
    }
else if(*D<=-DFF[3])
   {
    Dn=-2;
    DF[0]=FMAX;
   }
else if(*D>=DFF[3])
   {
   Dn=3;
   DF[0]=0;
   }
DF[1]=FMAX-DF[0];
/*使用误差范围优化后的规则表rule[7][7]*/
/*输出值使用13个隶属函数,中心值由UFF[7]指定*/
/*一般都是四个规则有效*/
Un[0]=rule[Pn-1+3][Dn-1+3];
Un[1]=rule[Pn+3][Dn-1+3];
Un[2]=rule[Pn-1+3][Dn+3];
Un[3]=rule[Pn+3][Dn+3];
if(PF[0]<=DF[0])
   UF[0]=PF[0];
else
   UF[0]=DF[0];
if(PF[1]<=DF[0])
   UF[1]=PF[1];
else
   UF[1]=DF[0];
if(PF[0]<=DF[1])
   UF[2]=PF[0];
else
   UF[2]=DF[1];
if(PF[1]<=DF[1])
   UF[3]=PF[1];
else
   UF[3]=DF[1];
/*同隶属函数输出语言值求大*/

if(Un[0]==Un[1])
{
   if(UF[0]>UF[1])
    UF[1]=0;
   else
    UF[0]=0;
}
if(Un[0]==Un[2])
{
   if(UF[0]>UF[2])
    UF[2]=0;
   else
    UF[0]=0;
}
if(Un[0]==Un[3])
{
   if(UF[0]>UF[3])
    UF[3]=0;
   else
    UF[0]=0;
}
if(Un[1]==Un[2])
{
   if(UF[1]>UF[2])
    UF[2]=0;
   else
    UF[1]=0;
}
if(Un[1]==Un[3])
{
   if(UF[1]>UF[3])
    UF[3]=0;
   else
    UF[1]=0;
}
if(Un[2]==Un[3])
{
   if(UF[2]>UF[3])
    UF[3]=0;
   else
    UF[2]=0;
}

/*重心法反模糊*/
/*Un[]原值为输出隶属函数的标号，转换为隶属函数值*/
if(Un[0]>=0)
   Un[0]=UFF[Un[0]];
else
   Un[0]=-UFF[-Un[0]];
if(Un[1]>=0)
   Un[1]=UFF[Un[1]];
else
   Un[1]=-UFF[-Un[1]];
if(Un[2]>=0)
   Un[2]=UFF[Un[2]];
else
   Un[2]=-UFF[-Un[2]];
if(Un[3]>=0)
   Un[3]=UFF[Un[3]];
else
   Un[3]=-UFF[-Un[3]];

temp1=UF[0]*Un[0]+UF[1]*Un[1]+UF[2]*Un[2]+UF[3]*Un[3];
temp2=UF[0]+UF[1]+UF[2]+UF[3];
U=temp1/temp2;
if(U<0)
	return -U;
else
	return U;
}
