zengwangfa/2019-Electronic-Design-Competition/others/software for rail gun/rt-thread-master/bsp/stm32f40x/applications/ioDevices.h

#ifndef __IO_DEVICES_H
#define __IO_DEVICES_H

#include "DataType.h"
typedef struct 
{
		uint8 time;
		uint8 count;
		uint8 number;	
}Buzzer_Type;

uint8 get_boma_value(void);
uint8 is_wifi_connect(void);

void key_down(void *args);

void Buzzer_Init(void);
	
void buzzer_once(void);

/* count为响的次数  length响的时间长度  */
void Buzzer_Set(Buzzer_Type* buzzer,uint8 count,uint8 length);

void Buzzer_Process(Buzzer_Type * buzzer);

extern Buzzer_Type Beep;

void rail_gun_start_charge(void);

void rail_gun_start_up(void);

#endif
