zengwangfa/2019-Electronic-Design-Competition/others/software for development board/rt-thread-master/bsp/stm32f40x/User/DataProcess.h

#ifndef __DATA_PROCESS_H_
#define __DATA_PROCESS_H_

#include "DataType.h"

typedef struct
{
	uint8 Status;      //检测时状态
	uint8 ShortStatus; //短路的状态
	uint8 Finish_Flag;  //读取完成的标志
	uint8 PaperNumber;  //纸张数量
	float Capacitance;
	
	int Time; //时间

	
}PaperCountEngine_Type;//纸张测数器状态



void get_capcity_value(void);

/* 【校准时】获取单极板 容值 */
float get_single_capacity(void);

void FDC2214_Data_Adjust(void);//数据校准

void	Capcity_Paper_Detection(void); //获取电容值

int	Short_Circuit_Detection(void);//短路检测

void DataSubsection(float Cap_Division[],float arrey[],int Number);

uint8 ProbablityCapacitance(float CompareArrey[])	;


extern float Cap_Division[100];/**/
extern int   Cap_Probability[100]; //存放可能性

extern int HMI_Debug_Write_Button;
extern int HMI_Work_Button;

extern PaperCountEngine_Type Paper; //SB
extern int ShortFlag;        //短路标志位


extern float KT_Board_Value_In_Flash; //KT板Flash数值
extern float Fiber_Board_Value_In_Flash;//纤维板 Flash数值


/* 打印机 纸张检测 */
void Printer_Paper_Detection(void);

/* 材料 检测 */
void Material_Detection(void);

#endif
