zengwangfa/2019-Electronic-Design-Competition/others/software for development board/rt-thread-master/bsp/stm32f40x/User/init.h

#ifndef __INIT_H_
#define __INIT_H_



#include "sys.h" 

#include "led.h"
#include "drv_oled.h"
#include "oled.h"
#include "gyroscope.h"
#include "drv_adc.h"
#include "drv_pwm.h"

#include "DataType.h"


/*---------------------- Constant / Macro Definitions -----------------------*/		

/************重要定义****************/






void rt_hw_us_delay(uint32 us);
void rt_hw_ms_delay(uint32 ms);
void delay_us(uint32 nTimer);

int sprintf(char *buf, const char *format, ...);


#endif
