zengwangfa/2019-Electronic-Design-Competition/others/software for development board/rt-thread-master/bsp/stm32f40x/applications/light.c

#define LOG_TAG    "light"

#include "light.h"
#include <rtthread.h>
#include <elog.h>
#include "sys.h"
#include <stdlib.h>
#include "drv_pwm.h"
#include <drivers/pin.h>

short light_value = 0;

/*******************************************
* 函 数 名：Light_Output_Limit
* 功    能：灯光亮度输出限制
* 输入参数：灯光亮度值 0~90%
* 返 回 值：None
* 注    意：
********************************************/
int Light_Output_Limit(short *value)
{
		*value = *value >= 90 ? 90 : *value ;//限幅
		*value = *value <= 0  ? 0   : *value ;//限幅
		return *value;
}



/**
  * @brief  Light_Control(探照灯控制)
  * @param  控制指令 0x00：不动作  0x01：向上  0x02：向下
  * @retval None
  * @notice 
  */

void Search_Light_Control(uint8 *action)
{
		switch(*action)
		{
				case 0x01:light_value += 5; //变亮
									break;  		
				case 0x02:light_value -= 5; //变暗
									break;  
				default: break;
		}
		Light_Output_Limit(&light_value);
		TIM10_PWM_CH1_F6(light_value);
		TIM11_PWM_CH1_F7(light_value);
		*action = 0x00; //清除控制字
}




/*【探照灯】 修改 【当前】 MSH方法 */
static int light(int argc, char **argv)
{
    int result = 0;
    if (argc != 2){
        log_e("Error! Proper Usage: YunTai_medvalue_set 2000");
				result = -RT_ERROR;
        goto _exit;
    }

		if(atoi(argv[1]) <= 100 ){		
				light_value = atoi(argv[1]) ;
				log_i("Light Value:  %d",light_value);
		}
		else {
				log_e("Error! The value is out of range!");
		}
_exit:
    return result;
}
MSH_CMD_EXPORT(light,ag: light <0~100>);
