zengwangfa/2019-Electronic-Design-Competition/others/software for development board/rt-thread-master/bsp/stm32f40x/applications/rc_data.h

#ifndef __RC_DATA_H_
#define __RC_DATA_H_

#include "DataType.h"

typedef struct{

		int16 X;    //摇杆 X、Y轴模拟量 （X正方向为机头方向）
		int16 Y;
		int16 Z;    //Z为垂直方向
		int16 Fx;   //转换的 X轴分力
		int16 Fy;   //转换的 Y轴分力
		int16 Yaw;  //偏航
		int16 Force;//合力
		float Angle;//合力的角度
}Rocker_Type;

typedef struct{
		uint16  THR;
		uint16  YAW;
		uint16  ROL;
		uint16  PIT;
	
}ReceiveData_Type;

typedef struct{
		uint8  All_Lock;       //总开关  
		uint8  Depth_Lock;     //【深度】	 0x01 深度锁定、0x02 人工控制 
		uint8  Direction_Lock; //【方向】	 0x01 方向锁定、0x02 随水动
		uint8  Move;      		 //【运动】	 0x01 前进、    0x02 后退、  0x00 不动作（默认）
		uint8  Translation;    //【平移】	 0x01 左平移、  0x02 右平移、0x00 不动作（默认）
	  uint8  Vertical;       //【垂直】	 0x01 向上、    0x02 向下、  0x00 不动作（默认）
		uint8  Rotate;         //【旋转】	 0x01 左旋、    0x02 右旋、  0x00表示不动作（默认）
		uint16 Power;          //【油门】	 0x00~0xff (0~255) 表示的油门大小：4档位可调，LB加档，LT减档，可分别设置4个档位油门大小
		uint8  Light;          //【灯光】	 0x01 打开、    0x00 关闭（默认）
		uint8  Focus;          //【聚焦】  0x01 聚焦、		0x02 放焦、  0x11 放大、0x12 缩小、0x00表示不动作（默认） 
		uint8  Yuntai;         //【云台】	 0x01 向上、    0x02 向下、  0x00表示不动作（默认）
		uint8  Arm;            //【机械臂】0x01 张开、    0x02 关闭、  0x00表示不动作（默认）
		uint8  Raspi;          //【树莓派】0x01 代表树莓派开机，0x00为无开机响应（默认）
		uint8  Reserve;        //【机械臂】0x01 张开、    0x02 关闭、  0x00表示不动作（默认）
}ControlCmd_Type;



extern Rocker_Type Rocker;
extern ControlCmd_Type ControlCmd;
extern ReceiveData_Type ReceiveData;
void Control_Cmd_Get(ControlCmd_Type *cmd); //控制命令获取
void Control_Cmd_Clear(ControlCmd_Type *cmd);//控制命令清零
void Remote_Control_Data_Analysis(uint8 Data); //控制数据解析

// is_raspi_start(树莓派是否开机)
uint8 is_raspi_start(void);
uint8 get_button_value(ControlCmd_Type *cmd);
#endif 
