zengwangfa/2019-Electronic-Design-Competition/others/software for development board/rt-thread-master/bsp/stm32f40x/applications/ret_data.h

#ifndef __RETURN_DATA_
#define __RETURN_DATA_

#include "DataType.h"


void Convert_Return_Computer_Data(Sensor_Type *Sensor); //返回上位机数据 转换

void Send_Buffer_Agreement(uint8 *begin_buff,uint8 *buff,uint8 len);

extern uint8 Return_Data[22];

extern uint8 device_hint_flag;		//设备提示字符




#endif
