zengwangfa/2019-Electronic-Design-Competition/others/software for development board/rt-thread-master/bsp/stm32f40x/drivers/drv_adc.h

#ifndef __ADC_CONVERT_H_
#define __ADC_CONVERT_H_

#include "DataType.h"



//初始化ADC															   
int adc_init(void);

uint16 get_adc2(uint8 ch);  //get adc通道值

uint16 get_adc1(uint8 ch); //get adc3通道值

float get_voltage_value(void); //get 电压值

float get_current_value(void);// get电流值 

#endif
