zengwangfa/2019-Electronic-Design-Competition/others/software for development board/rt-thread-master/bsp/stm32f40x/drivers/drv_i2c.h

#ifndef __MYIIC_H
#define __MYIIC_H
#include "sys.h" 
//////////////////////////////////////////////////////////////////////////////////	 
//本程序只供学习使用，未经作者许可，不得用于其它任何用途
//ALIENTEK STM32F407开发板
//IIC 驱动代码	   
//正点原子@ALIENTEK
//技术论坛:www.openedv.com
//创建日期:2014/5/6
//版本：V1.0
//版权所有，盗版必究。
//Copyright(C) 广州市星翼电子科技有限公司 2014-2024
//All rights reserved									  
////////////////////////////////////////////////////////////////////////////////// 	
   	   		   
//IO方向设置
#define SDA_IN()  {GPIOE->MODER&=~(3<<(2*12));GPIOE->MODER|=0<<(2*12);}	//PB9输入模式  2*pin_number
#define SDA_OUT() {GPIOE->MODER&=~(3<<(2*12));GPIOE->MODER|=1<<(2*12);} //PB9输出模式
//IO操作函数	 
#define IIC_SCL    PEout(10) //SCL
#define IIC_SDA    PEout(12) //SDA	 
#define READ_SDA   PEin(12)  //输入SDA 

//IIC所有操作函数
void IIC_Init(void);                //初始化IIC的IO口				 
void IIC_Start(void);				//发送IIC开始信号
void IIC_Stop(void);	  			//发送IIC停止信号
void IIC_Send_Byte(u8 txd);			//IIC发送一个字节
u8 IIC_Read_Byte(unsigned char ack);//IIC读取一个字节
u8 IIC_Wait_Ack(void); 				//IIC等待ACK信号
void IIC_Ack(void);					//IIC发送ACK信号
void IIC_NAck(void);				//IIC不发送ACK信号

void IIC_Write_One_Byte(u8 daddr,u8 addr,u8 data);
u8 IIC_Read_One_Byte(u8 daddr,u8 addr);	  
#endif
