zengwangfa/2019-Electronic-Design-Competition/others/software for development board/rt-thread-master/bsp/stm32f40x/rtconfig.py

import os

# toolchains options
ARCH='arm'
CPU='cortex-m4'
CROSS_TOOL='keil'

if os.getenv('RTT_CC'):
    CROSS_TOOL = os.getenv('RTT_CC')

# cross_tool provides the cross compiler
# EXEC_PATH is the compiler execute path, for example, CodeSourcery, Keil MDK, IAR
if  CROSS_TOOL == 'gcc':
    PLATFORM 	= 'gcc'
    EXEC_PATH 	= r'E:/Program Files/CodeSourcery/Sourcery G++ Lite/bin'
elif CROSS_TOOL == 'keil':
    PLATFORM 	= 'armcc'
    EXEC_PATH 	= r'Z:\Software\Keil5'
elif CROSS_TOOL == 'iar':
    print('================ERROR============================')
    print('Not support iar yet!')
    print('=================================================')
    exit(0)

if os.getenv('RTT_EXEC_PATH'):
	EXEC_PATH = os.getenv('RTT_EXEC_PATH')

BUILD = 'debug'
STM32_TYPE = 'STM32F4XX'

if PLATFORM == 'gcc':
    # toolchains
    PREFIX = 'arm-none-eabi-'
    CC = PREFIX + 'gcc'
    AS = PREFIX + 'gcc'
    AR = PREFIX + 'ar'
    LINK = PREFIX + 'gcc'
    TARGET_EXT = 'elf'
    SIZE = PREFIX + 'size'
    OBJDUMP = PREFIX + 'objdump'
    OBJCPY = PREFIX + 'objcopy'

    DEVICE = '  -mcpu=cortex-m4 -mthumb -mfpu=fpv4-sp-d16 -mfloat-abi=hard -ffunction-sections -fdata-sections'
    CFLAGS = DEVICE + ' -g -Wall -DSTM32F407ZG -DSTM32F4XX -DUSE_STDPERIPH_DRIVER -D__ASSEMBLY__ -D__FPU_USED'
    AFLAGS = ' -c' + DEVICE + ' -x assembler-with-cpp -Wa,-mimplicit-it=thumb '
    LFLAGS = DEVICE + ' -lm -lgcc -lc' + ' -nostartfiles -Wl,--gc-sections,-Map=rtthread-stm32.map,-cref,-u,Reset_Handler -T stm32_rom.ld'

    CPATH = ''
    LPATH = ''

    if BUILD == 'debug':
        CFLAGS += ' -O0 -gdwarf-2'
        AFLAGS += ' -gdwarf-2'
    else:
        CFLAGS += ' -O2'

    POST_ACTION = OBJCPY + ' -O binary $TARGET rtthread.bin\n' + SIZE + ' $TARGET \n'

elif PLATFORM == 'armcc':
    # toolchains
    CC = 'armcc'
    AS = 'armasm'
    AR = 'armar'
    LINK = 'armlink'
    TARGET_EXT = 'axf'

    DEVICE = ' --cpu=cortex-m4.fp'
    CFLAGS = DEVICE + ' --apcs=interwork -DUSE_STDPERIPH_DRIVER -DSTM32F40_41xxx'
    AFLAGS = DEVICE
    LFLAGS = DEVICE + ' --info sizes --info totals --info unused --info veneers --list rtthread-stm32.map --scatter stm32_rom.sct'

    CFLAGS += ' -I' + EXEC_PATH + '/ARM/RV31/INC'
    LFLAGS += ' --libpath ' + EXEC_PATH + '/ARM/RV31/LIB'

    EXEC_PATH += '/arm/bin40/'

    if BUILD == 'debug':
        CFLAGS += ' -g -O0'
        AFLAGS += ' -g'
    else:
        CFLAGS += ' -O2'

    POST_ACTION = 'fromelf --bin $TARGET --output rtthread.bin \nfromelf -z $TARGET'

elif PLATFORM == 'iar':
    # toolchains
    CC = 'iccarm'
    AS = 'iasmarm'
    AR = 'iarchive'
    LINK = 'ilinkarm'
    TARGET_EXT = 'out'

    DEVICE = ' -D USE_STDPERIPH_DRIVER' + ' -D STM32F10X_HD'

    CFLAGS = DEVICE
    CFLAGS += ' --diag_suppress Pa050'
    CFLAGS += ' --no_cse' 
    CFLAGS += ' --no_unroll' 
    CFLAGS += ' --no_inline' 
    CFLAGS += ' --no_code_motion' 
    CFLAGS += ' --no_tbaa' 
    CFLAGS += ' --no_clustering' 
    CFLAGS += ' --no_scheduling' 
    CFLAGS += ' --debug' 
    CFLAGS += ' --endian=little' 
    CFLAGS += ' --cpu=Cortex-M4' 
    CFLAGS += ' -e' 
    CFLAGS += ' --fpu=None'
    CFLAGS += ' --dlib_config "' + EXEC_PATH + '/arm/INC/c/DLib_Config_Normal.h"'    
    CFLAGS += ' -Ol'    
    CFLAGS += ' --use_c++_inline'
        
    AFLAGS = ''
    AFLAGS += ' -s+' 
    AFLAGS += ' -w+' 
    AFLAGS += ' -r' 
    AFLAGS += ' --cpu Cortex-M4' 
    AFLAGS += ' --fpu None' 

    LFLAGS = ' --config stm32f10x_flash.icf'
    LFLAGS += ' --redirect _Printf=_PrintfTiny' 
    LFLAGS += ' --redirect _Scanf=_ScanfSmall' 
    LFLAGS += ' --entry __iar_program_start'    

    EXEC_PATH = EXEC_PATH + '/arm/bin/'
    POST_ACTION = ''
